Jstudner/jcorp-nomad/SD_Card_Template/Books/All Top Comics 6.jpg

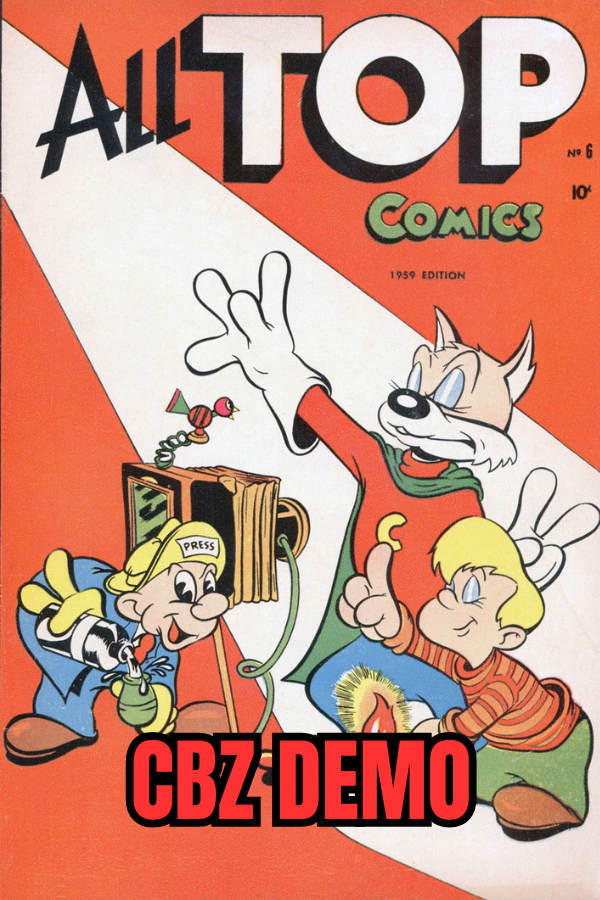
SD_Card_Template/Books/All Top Comics 6.jpg
