Jstudner/jcorp-nomad/SD_Card_Template/Books/MobyDick.jpg

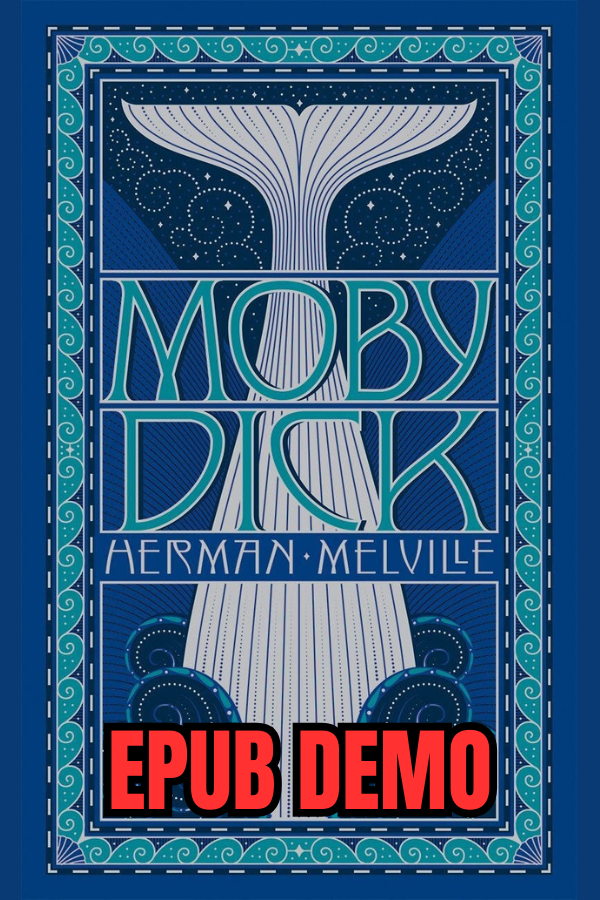
SD_Card_Template/Books/MobyDick.jpg
