Jstudner/jcorp-nomad/SD_Card_Template/Books/TheIliad.jpg

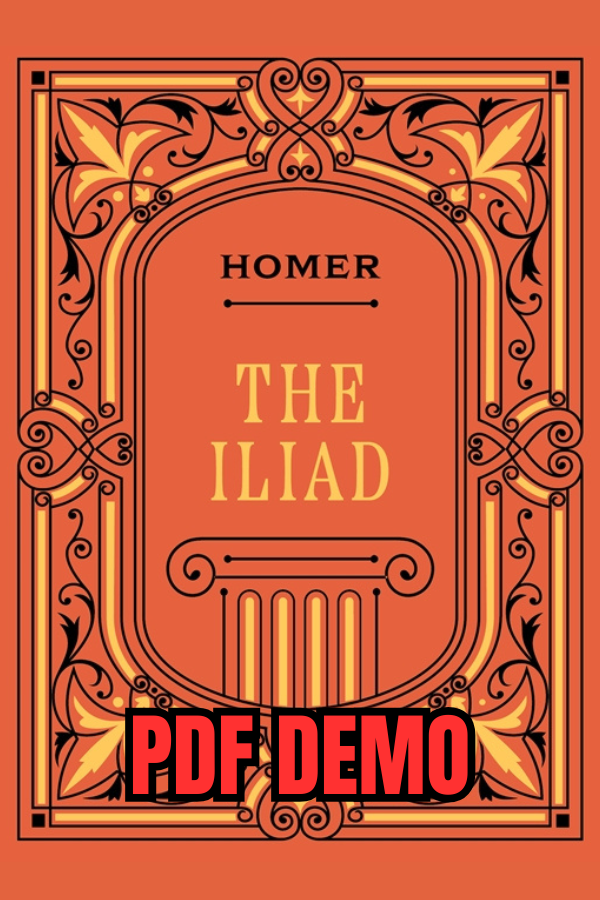
SD_Card_Template/Books/TheIliad.jpg
