Jstudner/jcorp-nomad/SD_Card_Template/Games/2048.png

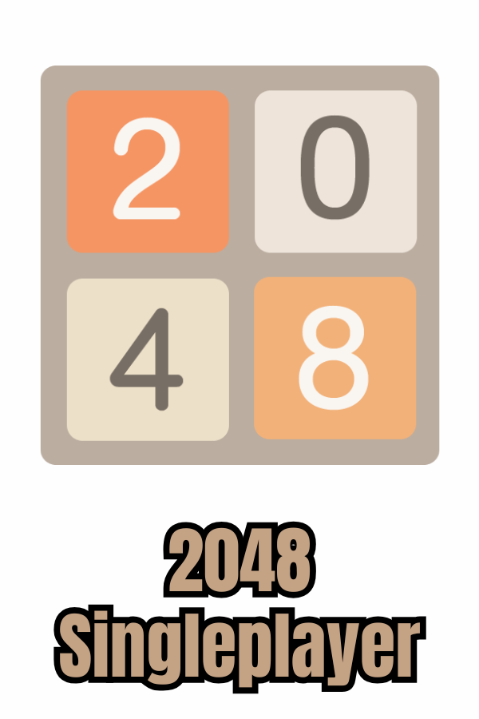
SD_Card_Template/Games/2048.png
