Jstudner/jcorp-nomad/SD_Card_Template/Games/Chess.png

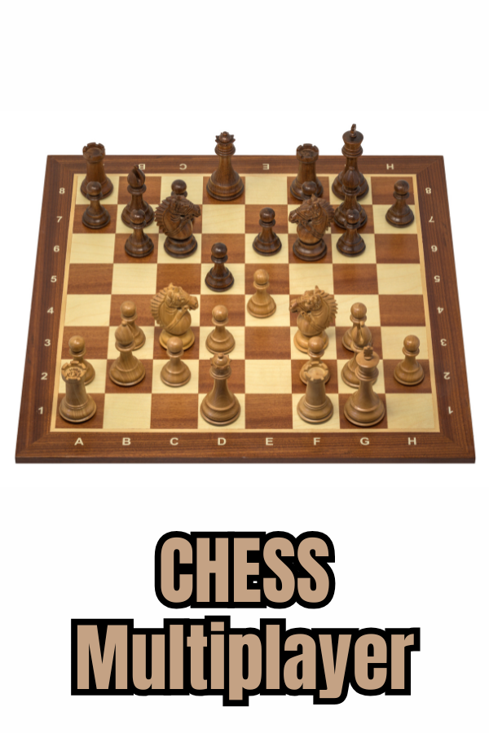
SD_Card_Template/Games/Chess.png
