Jstudner/jcorp-nomad/SD_Card_Template/Games/Connect Four.png

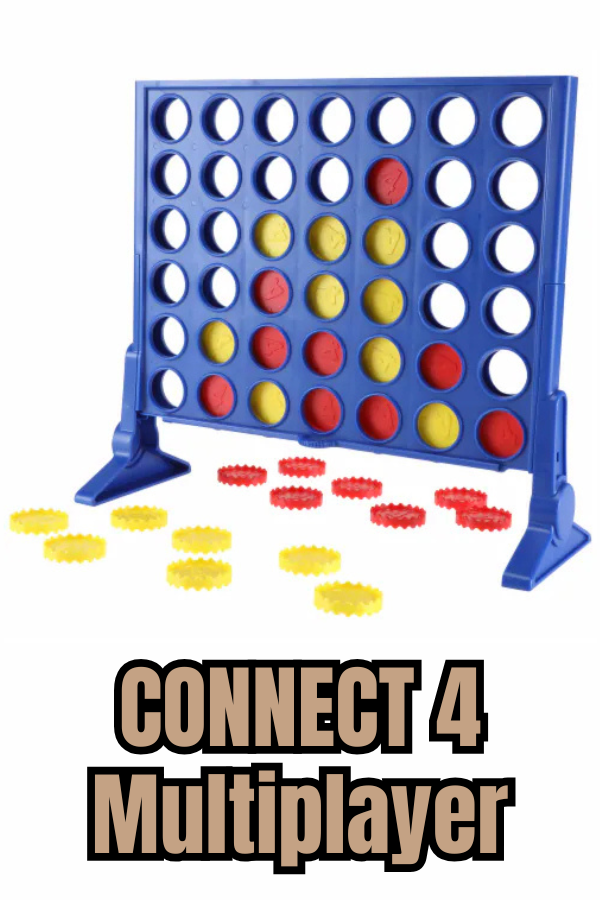
SD_Card_Template/Games/Connect Four.png
