Jstudner/jcorp-nomad/SD_Card_Template/Games/Crazy Eights.png

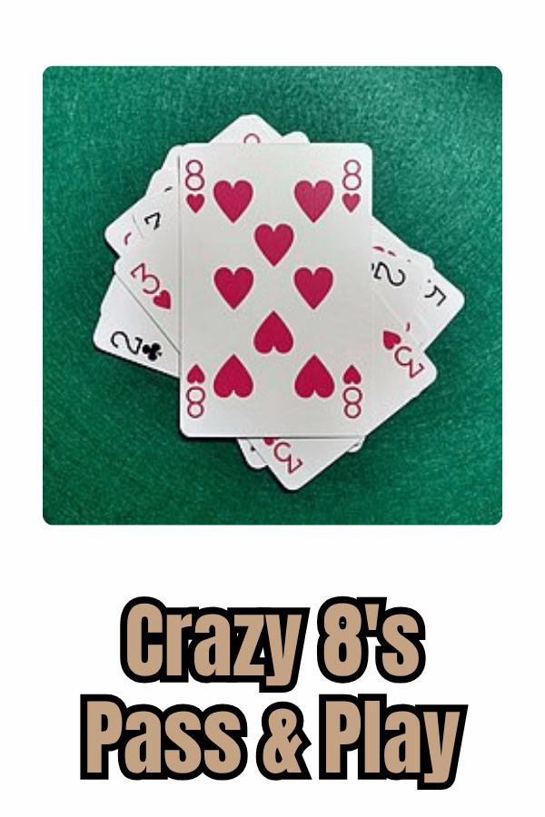
SD_Card_Template/Games/Crazy Eights.png
