Jstudner/jcorp-nomad/SD_Card_Template/Games/Doom.png

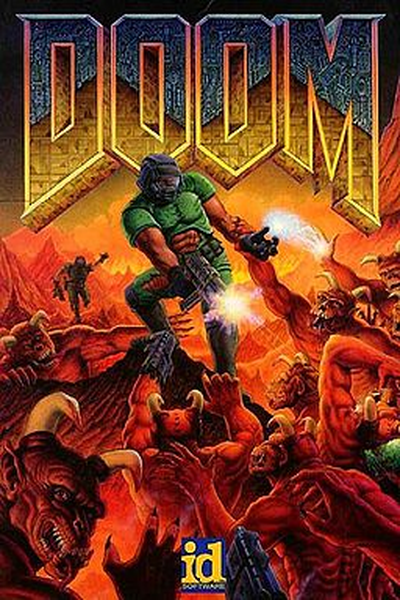
SD_Card_Template/Games/Doom.png
