Jstudner/jcorp-nomad/SD_Card_Template/Games/Dots and Boxes.png

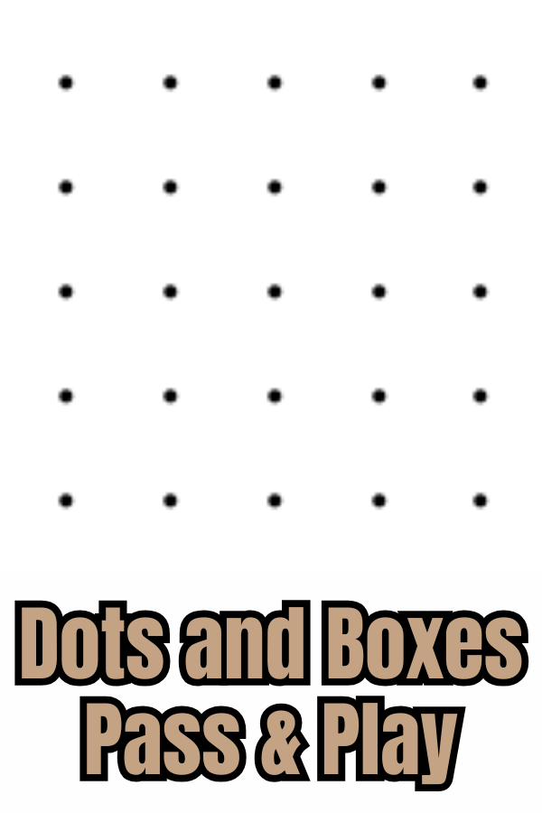
SD_Card_Template/Games/Dots and Boxes.png
