Jstudner/jcorp-nomad/SD_Card_Template/Games/Go.png

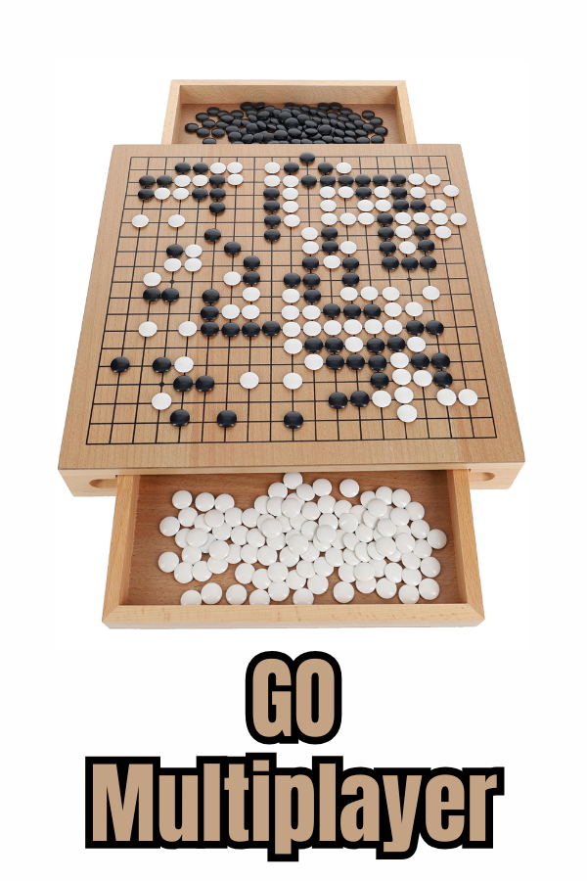
SD_Card_Template/Games/Go.png
