Jstudner/jcorp-nomad/SD_Card_Template/Games/Minesweeper.png

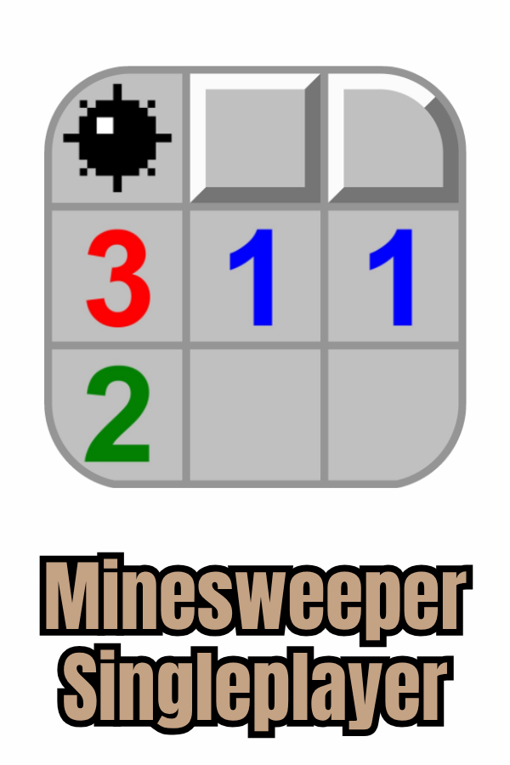
SD_Card_Template/Games/Minesweeper.png
