Jstudner/jcorp-nomad/SD_Card_Template/Games/Snake.png

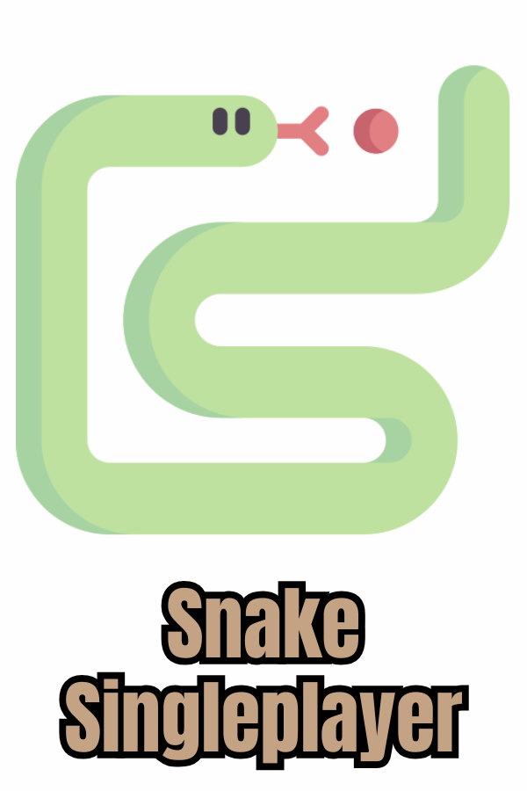
SD_Card_Template/Games/Snake.png
