Jstudner/jcorp-nomad/SD_Card_Template/Games/Tic-Tac-Toe.png

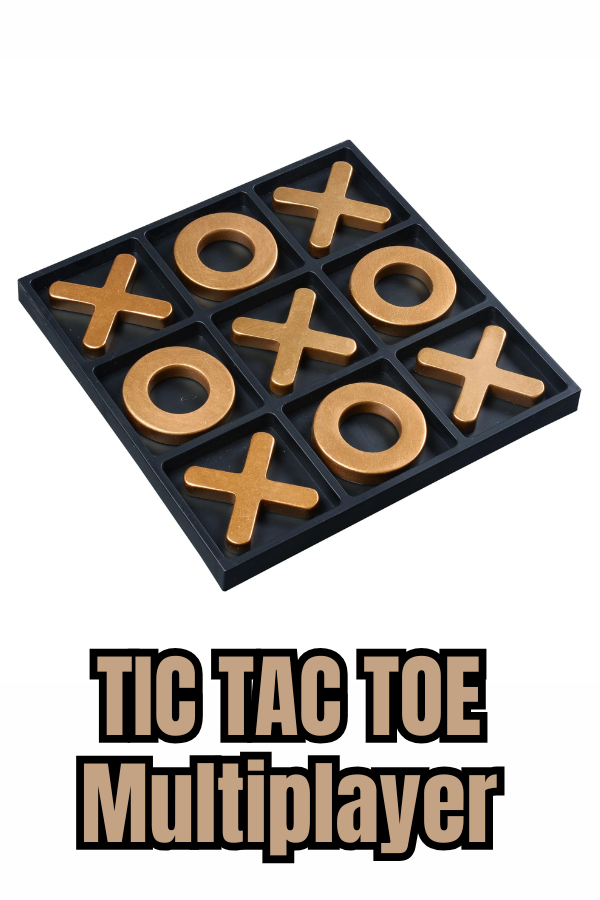
SD_Card_Template/Games/Tic-Tac-Toe.png
