Jstudner/jcorp-nomad/SD_Card_Template/Games/Whiteboard.png

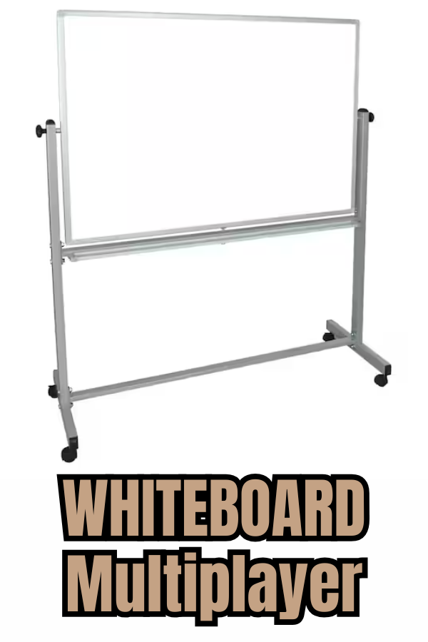
SD_Card_Template/Games/Whiteboard.png
