Jstudner/jcorp-nomad/SD_Card_Template/Maps/dc/tiles/10/292/391.jpg

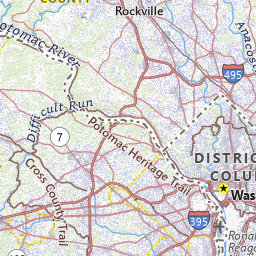
SD_Card_Template/Maps/dc/tiles/10/292/391.jpg
