Jstudner/jcorp-nomad/SD_Card_Template/Maps/dc/tiles/10/292/392.jpg

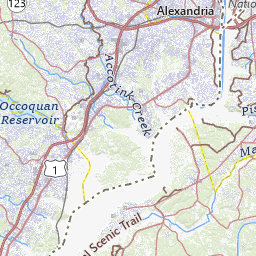
SD_Card_Template/Maps/dc/tiles/10/292/392.jpg
