Jstudner/jcorp-nomad/SD_Card_Template/Maps/dc/tiles/11/585/782.jpg

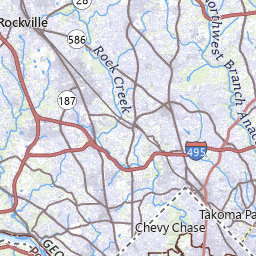
SD_Card_Template/Maps/dc/tiles/11/585/782.jpg
