Jstudner/jcorp-nomad/SD_Card_Template/Maps/dc/tiles/11/586/783.jpg

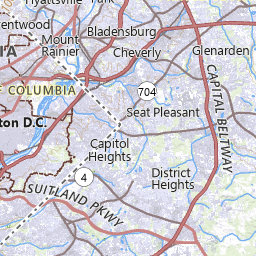
SD_Card_Template/Maps/dc/tiles/11/586/783.jpg
