Jstudner/jcorp-nomad/SD_Card_Template/Maps/dc/tiles/12/1170/1566.jpg

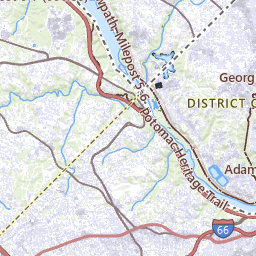
SD_Card_Template/Maps/dc/tiles/12/1170/1566.jpg
