Jstudner/jcorp-nomad/SD_Card_Template/Maps/dc/tiles/12/1171/1567.jpg

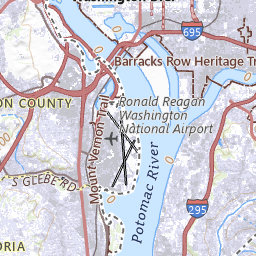
SD_Card_Template/Maps/dc/tiles/12/1171/1567.jpg
