Jstudner/jcorp-nomad/SD_Card_Template/Maps/dc/tiles/12/1172/1568.jpg

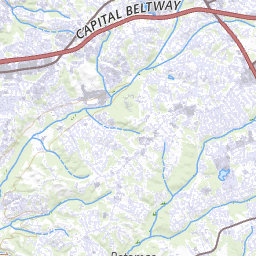
SD_Card_Template/Maps/dc/tiles/12/1172/1568.jpg
