Jstudner/jcorp-nomad/SD_Card_Template/Maps/dc/tiles/13/2342/3133.jpg

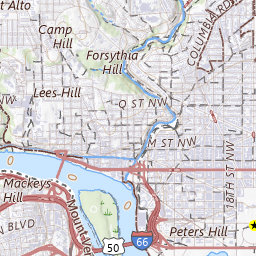
SD_Card_Template/Maps/dc/tiles/13/2342/3133.jpg
