Jstudner/jcorp-nomad/SD_Card_Template/Maps/dc/tiles/13/2344/3132.jpg

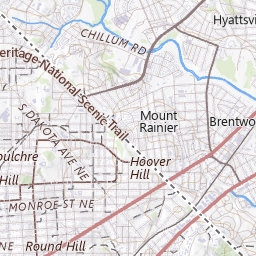
SD_Card_Template/Maps/dc/tiles/13/2344/3132.jpg
