Jstudner/jcorp-nomad/SD_Card_Template/Maps/dc/tiles/13/2345/3136.jpg

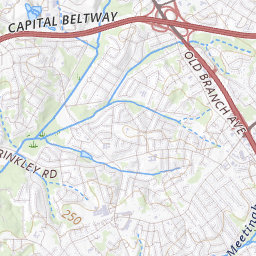
SD_Card_Template/Maps/dc/tiles/13/2345/3136.jpg
