Jstudner/jcorp-nomad/SD_Card_Template/Maps/dc/tiles/14/4683/6265.jpg

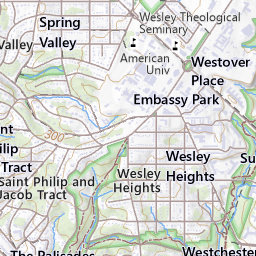
SD_Card_Template/Maps/dc/tiles/14/4683/6265.jpg
