Jstudner/jcorp-nomad/SD_Card_Template/Maps/dc/tiles/14/4684/6271.jpg

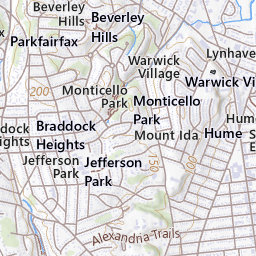
SD_Card_Template/Maps/dc/tiles/14/4684/6271.jpg
