Jstudner/jcorp-nomad/SD_Card_Template/Maps/dc/tiles/14/4686/6267.jpg

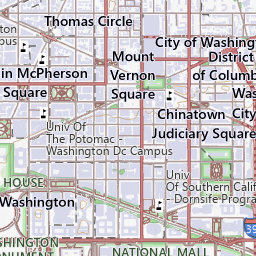
SD_Card_Template/Maps/dc/tiles/14/4686/6267.jpg
