Jstudner/jcorp-nomad/SD_Card_Template/Maps/dc/tiles/14/4687/6262.jpg

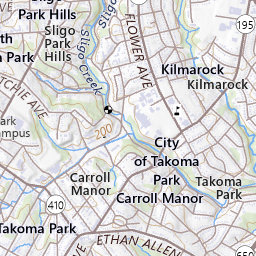
SD_Card_Template/Maps/dc/tiles/14/4687/6262.jpg
