Jstudner/jcorp-nomad/SD_Card_Template/Maps/dc/tiles/14/4688/6270.jpg

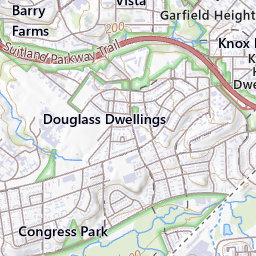
SD_Card_Template/Maps/dc/tiles/14/4688/6270.jpg
