Jstudner/jcorp-nomad/SD_Card_Template/Maps/dc/tiles/14/4689/6269.jpg

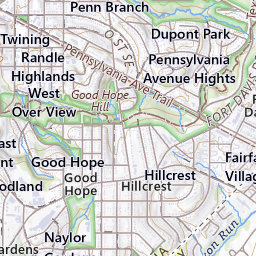
SD_Card_Template/Maps/dc/tiles/14/4689/6269.jpg
