Jstudner/jcorp-nomad/SD_Card_Template/Maps/dc/tiles/14/4691/6264.jpg

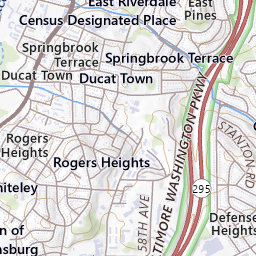
SD_Card_Template/Maps/dc/tiles/14/4691/6264.jpg
