Jstudner/jcorp-nomad/SD_Card_Template/Maps/dc/tiles/14/4691/6272.jpg

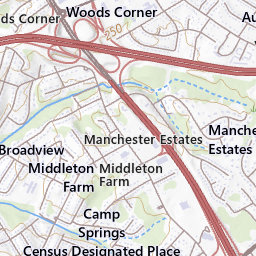
SD_Card_Template/Maps/dc/tiles/14/4691/6272.jpg
