Jstudner/jcorp-nomad/SD_Card_Template/Movies/The Phantom of The Opera.jpg

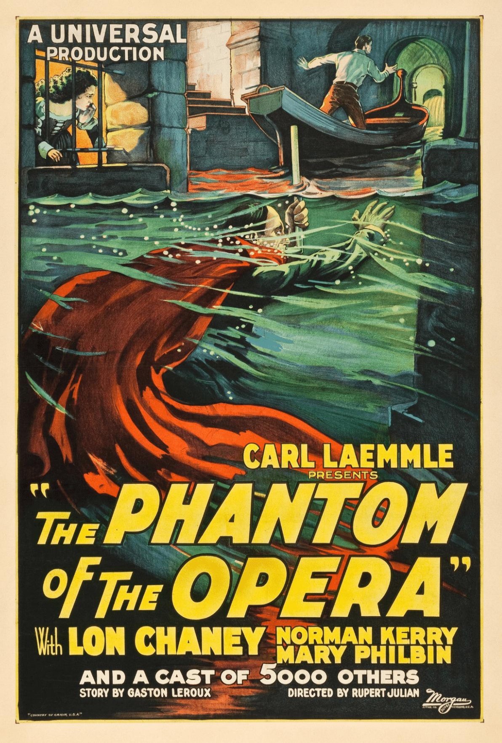
SD_Card_Template/Movies/The Phantom of The Opera.jpg
