Jstudner/jcorp-nomad/firmware/JcorpNomadProject/JcorpNomadProject.ino

// Jcorp Nomad Backend - exFAT edition
//<!-- Version 4.6 -->
//
// ---------------- board variant: set it in Display_ST7789.h ----------------
// USB-A, Waveshare ESP32-S3-LCD-1.47:  backlight GPIO 48, BOARD_USB_C 0 (default)
// USB-C, Waveshare ESP32-S3-LCD-1.47B: backlight GPIO 46, BOARD_USB_C 1
//
// that pin is the only firmware-visible difference between the two boards, and this
// file is byte-identical for both - checked against the flashing site's build tree.
//
// setting it here instead does nothing, and does it silently. the pin is used only in
// Display_ST7789.cpp, which is its own translation unit, so a define in the sketch
// never reaches it: with the define here Display_ST7789.cpp.o comes out identical to
// an unflagged build, the board keeps GPIO 48 and the screen just stays dark. edit the
// one line in Display_ST7789.h, or build with -DBOARD_USB_C=1.
#include <Arduino.h>
#include <WiFi.h>
#include <esp_netif.h>
#include <esp_heap_caps.h>
#include <AsyncTCP.h>
#include <ESPAsyncWebServer.h>
// NomadSD replaces SD_MMC: same pins and peripheral, SdFat underneath, so exFAT,
// FAT32 and FAT16 all mount. Included early because StreamHandle below holds a
// NomadFile64. NomadSD.h hides SdFat's headers, whose global `typedef FsFile File`
// would collide with fs::File.
#include "NomadSD.h"
#include "NomadDLNA.h"
#define SD_MMC NomadSD
#ifndef SD
#define SD NomadSD
#endif
#include "NomadDNS.h"
#include <ESPmDNS.h>
#include <ArduinoJson.h>
#include <map>
#include <time.h>
#include "Display_ST7789.h"
#include "LVGL_Driver.h"
#include "ui.h" 
#include "RGB_lamp.h"
#include <SPIFFS.h>
#include <Preferences.h>
#include "esp_wifi.h"
#include "esp_netif.h"      // esp_netif_dhcps_* -- restart softAP DHCP if it stays down (issue #126)
#include "esp_heap_caps.h"  // heap_caps_get_* -- DHCP-start heap logging
#if defined(ARDUINO_ARCH_ESP32)
  #include "soc/soc.h"
  #include "soc/rtc_cntl_reg.h"
  #include "esp_system.h"
  #include "esp_core_dump.h"
#endif
#include "esp32-hal-tinyusb.h"  // usb_persist_restart: the reliable road into ROM download mode
#include "usb_mode.h"
#include "boot_mode.h" // library for firmware switching

struct BreakdownStats {
  uint64_t bytes = 0;
  uint32_t files = 0;
  uint32_t dirs = 0;
};

void handleRangeRequest(AsyncWebServerRequest *request);
String urlDecode(const String& str);
void enqueueIndexUpdateForPath(const String& path);
void RGB_SetMode(uint8_t mode);
void applyRGBSettings();
String sanitizeToken(const String &s);
bool saveSettings();
String humanSize(size_t bytes);
extern void usb_setup();
extern void usb_loop();
#define BOOT_BUTTON_PIN 0
#include <vector>
#include <algorithm>
#include <atomic>
#ifndef GLOBAL_INDEX_BUF
#define GLOBAL_INDEX_BUF 1024
#endif
enum { HALF_INDEX_BUF = GLOBAL_INDEX_BUF / 2 };

static char g_lineBuf[GLOBAL_INDEX_BUF];
static uint8_t g_fileBuf[4096];                 // file reads/writes
static std::map<String, unsigned long> g_lastIndexSkipLog;
static inline void freeString(String &s) { s = String(); }
static inline void freeVectorString(std::vector<String> &v) { std::vector<String>().swap(v); }
static inline void freeVectorUInt32(std::vector<uint32_t> &v) { std::vector<uint32_t>().swap(v); }
static inline void closeFile(File &f) { if (f) f.close(); }

struct LvglMsg {
  char text[80];
  bool show;
};
static QueueHandle_t lvglQueue = NULL;

static void lvglSendMsg(const char *text, bool show) {
  if (!lvglQueue) return;
  LvglMsg m;
  m.show = show;
  if (text) {
    strncpy(m.text, text, sizeof(m.text) - 1);
    m.text[sizeof(m.text) - 1] = '\0';
  } else {
    m.text[0] = '\0';
  }
  xQueueSend(lvglQueue, &m, pdMS_TO_TICKS(50));
}

static void lvglDrainQueue() {
  if (!lvglQueue) return;
  LvglMsg msg;
  bool drainedAny = false;
  bool endedHidden = false;
  while (xQueueReceive(lvglQueue, &msg, 0) == pdTRUE) {
    if (msg.show) {
      lv_obj_clear_flag(ui_MediaGen, LV_OBJ_FLAG_HIDDEN);
      lv_textarea_set_text(ui_MediaGen, msg.text);
      endedHidden = false;
    } else {
      lv_textarea_set_text(ui_MediaGen, "");
      lv_obj_add_flag(ui_MediaGen, LV_OBJ_FLAG_HIDDEN);
      endedHidden = true;
    }
    drainedAny = true;
  }
  //only redraws the screen after all updates are done, removed the spinner (reloading constantly.. whoops lol)
  if (drainedAny) {
    // if we just hid the overlay, redraw twice so no remnant is left behind
    if (endedHidden) {
      lv_obj_invalidate(lv_scr_act());
      lv_timer_handler();
    }
    lv_timer_handler();
  }
}

static volatile bool bootButtonPressed = false;
// /flash-mode sets this; loop() does the actual switch (LVGL + restart must
// not run on the async_tcp task)
static volatile bool g_enterFlashMode = false;
#ifndef INDEX_MIN_HEAP
#define INDEX_MIN_HEAP 15000UL
#endif
static inline bool enoughHeapForIndex(size_t estNeededBytes = 20000) {
  size_t freeHeap = ESP.getFreeHeap();
  if (freeHeap < (INDEX_MIN_HEAP + estNeededBytes)) {
    Serial.printf("[Index] Not enough heap for index work (free=%u, need~%u). Deferring.\n",
                  (unsigned)freeHeap, (unsigned)(INDEX_MIN_HEAP + estNeededBytes));
    return false;
  }
  return true;
}
static size_t jsonEscapeToBuf(const String &in, char *dst, size_t dstLen) {
  if (!dst || dstLen == 0) return 0;
  size_t pos = 0;
  for (size_t i = 0; i < in.length() && pos + 1 < dstLen; ++i) {
    char c = in.charAt(i);
    if (c == '\\' || c == '\"') {
      if (pos + 2 >= dstLen) break;
      dst[pos++] = '\\';
      dst[pos++] = c;
    } else if (c == '\n') {
      if (pos + 2 >= dstLen) break;
      dst[pos++] = '\\';
      dst[pos++] = 'n';
    } else if (c == '\r') {
      if (pos + 2 >= dstLen) break;
      dst[pos++] = '\\';
      dst[pos++] = 'r';
    } else {
      dst[pos++] = c;
    }
  }
  dst[pos] = '\0';
  return pos;
}

static void writeIndexEntryToFile(File &fout, char t, const String &name, const String &path, uint64_t sz = 0, uint64_t mt = 0) {
  char escName[HALF_INDEX_BUF];
  char escPath[HALF_INDEX_BUF];
  jsonEscapeToBuf(name, escName, HALF_INDEX_BUF);
  jsonEscapeToBuf(path, escPath, HALF_INDEX_BUF);

  int pos = snprintf(g_lineBuf, GLOBAL_INDEX_BUF,
                     "{\"t\":\"%c\",\"n\":\"%s\",\"p\":\"%s\"", t, escName, escPath);
  if (pos < 0) pos = 0;
  if (t == 'f') {
    pos += snprintf(g_lineBuf + pos, (pos < (int)GLOBAL_INDEX_BUF) ? (GLOBAL_INDEX_BUF - pos) : 0,
                    ",\"sz\":%llu,\"mt\":%llu}\n",
                    (unsigned long long)sz, (unsigned long long)mt);
  } else {
    pos += snprintf(g_lineBuf + pos, (pos < (int)GLOBAL_INDEX_BUF) ? (GLOBAL_INDEX_BUF - pos) : 0,
                    "}\n");
  }

  size_t wlen = strlen(g_lineBuf);
  if (wlen) fout.write((const uint8_t*)g_lineBuf, wlen);
}
int screenBrightness = 100; // 0-100, default full brightness
void handleConnector(AsyncWebServerRequest *request);
unsigned long lastTempReading = 0;
float currentTempC = 0.0;
volatile bool mediaStreamingActive = false; // Flag to indicate active media streaming
volatile unsigned long lastStreamIoMs = 0;  // last time a streaming request/fill touched the SD
static bool sdScanned = false;
const uint32_t SD_SCAN_DELAY = 5000;  // milliseconds after boot
SemaphoreHandle_t sdMutex = NULL;
#include <map>
static uint32_t nextStreamId = 1;
// NomadFile64 rather than fs::File, so streams can seek and size past 4 GB on
// exFAT. Identical behaviour on FAT32. Move-only, like the SdFat handle.
struct StreamHandle {
  NomadFile64 file;
  String path;
  unsigned long lastActivity;
  uint64_t lastEndByte;
};
static std::map<uint32_t, StreamHandle> streamingFiles;
static std::map<String, uint32_t> streamPathIndex;
static SemaphoreHandle_t streamingFilesMutex = NULL;
static const int MAX_CONCURRENT_STREAMS = 8;

// close a handle we opened but never sent, so it doesn't leak until the LRU gets it
static void closeStreamById(uint32_t streamId) {
  if (!streamId) return;
  bool locked = (!streamingFilesMutex) ||
                (xSemaphoreTake(streamingFilesMutex, pdMS_TO_TICKS(300)) == pdTRUE);
  if (!locked) return;
  auto it = streamingFiles.find(streamId);
  if (it != streamingFiles.end()) {
    streamPathIndex.erase(it->second.path);
    it->second.file.close();
    streamingFiles.erase(it);
  }
  if (streamingFilesMutex) xSemaphoreGive(streamingFilesMutex);
}

static uint64_t cachedTotalBytes = 0;
static uint64_t cachedUsedBytes = 0;
static bool g_sdStatTrusted = false;
const char* SD_USAGE_FILE = "/.system-index/sd_usage.json";
static unsigned long lastScanTime = 0;
volatile bool sdbarDirty = false;
volatile int activeStreams = 0;
struct IndexBuildArgs {
  String dir;   // directory path to build index for (ex: "/Music/Album")
  String out;   // output index filename
};
static QueueHandle_t indexQueue = nullptr;

// Task management for performance optimization
TaskHandle_t indexWorkerTaskHandle = nullptr;
TaskHandle_t storageMonitorTaskHandle = nullptr;
volatile bool shutdownBackgroundTasks = false;
volatile bool indexingTasksActive = false;
String currentIndexingPath = "";
// Progress tracker for active indexing task
int g_currentBucketNum = 0;
int g_totalBucketsForProgress = 0;
int g_indexProgressPercent = 0;
SemaphoreHandle_t indexingPathMutex = NULL;

// ---- Multiplayer room store (HTTP polling, no WebSockets) ----
// Fixed-size plain char buffers, no Arduino String anywhere in this store or its
// handlers, and no SD I/O. Same class of hazard that caused heap corruption via
// unsynchronized Strings shared across tasks. Everything here is guarded by gameMutex.
#define MP_MAX_ROOMS 4
#define MP_CODE_LEN 5      // 4-char room code + NUL
#define MP_GAME_LEN 16     // e.g. "tictactoe", "chess"
#define MP_TOKEN_LEN 9     // 8 hex chars + NUL
#define MP_STATE_LEN 512   // opaque client-owned state blob (chess FEN ~90B, TTT ~32B)
#define MP_ROOM_IDLE_MS (2UL * 60UL * 1000UL)  // idle rooms are reclaimed after ~2 min

struct MpRoom {
  bool active;
  char code[MP_CODE_LEN];
  char game[MP_GAME_LEN];
  char token[2][MP_TOKEN_LEN];  // seat 0/1 tokens; empty string = seat open
  char state[MP_STATE_LEN];
  uint32_t seq;
  uint32_t games;               // finished games, used to alternate who starts a rematch
  unsigned long lastMs;
};
static MpRoom mpRooms[MP_MAX_ROOMS];
SemaphoreHandle_t gameMutex = NULL;

// Function declarations for task management
void shutdownBackgroundTasksForStreaming();
void startBackgroundTasksIfNeeded();
void checkStreamingTimeout();
void immediateEnqueueTopLevelTask(void *param);
void triggerIndexingIfNeeded(const String& filePath);
// Last time UI bar was updated
unsigned long lastSdbarUpdate = 0;
void updateSDBAR() {
  sdbarDirty = true;
}
void updateSDBAR_UI_ThreadOnly() {
  if (cachedTotalBytes == 0) return;
  
  int usage = (int)((cachedUsedBytes * 100) / cachedTotalBytes);
  if (usage > 100) usage = 100;
  if (usage < 0) usage = 0;
  
  lv_bar_set_value(ui_sdbar, usage, LV_ANIM_OFF);
  sdbarDirty = false;
}
#include <string> // used by std::map key
static std::map<std::string, unsigned long> lastIndexRequestMs;
const unsigned long INDEX_REQUEUE_COALESCE_MS = 2000UL; // 2 seconds coalescing
const size_t INDEX_REQUEST_MAP_EVICT_THRESHOLD = 200;       // prune once the map grows this large
const unsigned long INDEX_REQUEST_MAP_MAX_AGE_MS = 60000UL; // entries older than this are stale
static bool shouldCoalesceIndexRequest(const String &path) {
  std::string k(path.c_str());
  unsigned long now = millis();
  auto it = lastIndexRequestMs.find(k);
  if (it != lastIndexRequestMs.end()) {
    if (now - it->second < INDEX_REQUEUE_COALESCE_MS) {
      return false;
    }
  }
  lastIndexRequestMs[k] = now;

  if (lastIndexRequestMs.size() > INDEX_REQUEST_MAP_EVICT_THRESHOLD) {
    for (auto mit = lastIndexRequestMs.begin(); mit != lastIndexRequestMs.end(); ) {
      if (now - mit->second > INDEX_REQUEST_MAP_MAX_AGE_MS) {
        mit = lastIndexRequestMs.erase(mit);
      } else {
        ++mit;
      }
    }
  }
  return true;
}

// Helper: get parent directory for a path ("/Music/song.mp3" -> "/Music")
static String parentDirFromPath(const String &path) {
  if (path.length() == 0) return "/";
  int last = path.lastIndexOf('/');
  if (last <= 0) return "/"; // root or malformed -> treat as root
  String p = path.substring(0, last);
  if (p.length() == 0) return "/";
  return p;
}

// Paths that should never be indexed as media content. (generic SD card stuff that was causing some issues.)
static bool isFilesystemNoisePath(const String &path) {
  if (path.startsWith("/.system-index")) return true;      // our own index storage
  if (path.startsWith("/.")) return true;                  // hidden folders
  if (path.startsWith("/config")) return true;              // our own settings storage
  if (path.startsWith("/System Volume Information")) return true;
  if (path.startsWith("/$")) return true;                   // Windows/FAT system artifacts
  if (path.equalsIgnoreCase("/lost.dir")) return true;       // FAT filesystem recovery folder (Android/Linux)
  if (path.startsWith("/FOUND.")) return true;               // FAT32 chkdsk recovery folders (FOUND.000, FOUND.001, ...)
  if (path.equalsIgnoreCase("/RECYCLER")) return true;       // Windows recycle bin (older FAT)
  return false;
}

static bool shouldSkipIndexingPath(const String &path) {
  if (isFilesystemNoisePath(path)) return true;
  if (path.startsWith("/Archive")) return true;             // large ZIM archives, not media
  return false;
}

#define INDEXER_SLEEP_MS 300000 // 5 minutes between background scans
#define MAX_CLIENTS 8 // SoftAP max_connection; keep in sync with WiFi.softAP() calls below
String encodeIndexName(const String &path);

struct AdminSettings {
  String rgbMode = "off";
  String rgbColor = "#ff0000";
  String adminPassword = "";
  String wifiSSID = "Jcorp_Nomad";
  String wifiPassword = "password";
  int brightness = 100;            // percent 0-100 (Set_Backlight range); 230 was out-of-range and ignored
  bool autoGenerateMedia = true;   // check for new files on boot (default on)
  bool flipScreen = false;         // rotate LCD 180 deg (USB port upside down, e.g. car mounts)
  bool dlnaEnabled = true;         // TV support: DLNA server + SSDP discovery
  // WiFi Mode (station): join an existing network instead of running the hotspot.
  // staPersist=true -> try every boot (with hotspot fallback on failure).
  // staPersist=false -> only when the sta_once NVS flag is armed; a power cycle clears it.
  String staSSID = "";
  String staPassword = "";
  bool staPersist = false;
  // legacy wildcard captive DNS (answer every lookup with Nomad's address).
  // off = targeted responder, so phones keep using mobile data for the internet
  bool dnsCatchAll = false;
};

AdminSettings settings;
// Set by the /settings handler (async_tcp task); consumed by the task that owns
// LVGL flushes. MADCTL must never be written mid-flush from another task.
volatile bool lcdRotatePending = false;
const char* SETTINGS_PATH = "/config/settings.json";

// --- Admin session auth ---
// Not perfect, but designed to make it a bit more secure and properly gated, unlikly this will ever be needed, but some users want it as an option. 
String adminSessionToken = "";

String generateSessionToken() {
  char buf[33];
  for (int i = 0; i < 4; i++) {
    snprintf(buf + (i * 8), 9, "%08x", (unsigned)esp_random());
  }
  buf[32] = '\0';
  return String(buf);
}

bool isAdminAuthRequired() {
  return settings.adminPassword.length() > 0;
}

// Returns true if the request is allowed to perform an admin/state-changing action.
bool checkAdminAuth(AsyncWebServerRequest *request) {
  if (!isAdminAuthRequired()) return true; // admin password explicitly disabled
  if (adminSessionToken.length() == 0) return false; // nobody has logged in since boot
  if (!request->hasHeader("X-Admin-Token")) return false;
  return request->getHeader("X-Admin-Token")->value().equals(adminSessionToken);
}

// Web Console Logging System
#define MAX_LOG_ENTRIES 50
struct LogEntry {
  String message;
  String type;
  unsigned long timestamp;
};

LogEntry webLogs[MAX_LOG_ENTRIES];
int logIndex = 0;
int logCount = 0;
// guards webLogs[], lots of tasks write it and /console-logs reads it. unsynced
// String read/writes race the heap and panic. made in setup() before the server,
// so early boot logs (NULL mutex) skip locking safely
SemaphoreHandle_t webLogMutex = NULL;

// Function to add log entry for web console
void webLog(const String& message, const String& type = "info") {
  bool locked = (webLogMutex && xSemaphoreTake(webLogMutex, pdMS_TO_TICKS(50)) == pdTRUE);

  // if the reader has the lock, just go to serial instead of writing unsynced
  if (locked || !webLogMutex) {
    webLogs[logIndex].message = message;
    webLogs[logIndex].type = type;
    webLogs[logIndex].timestamp = millis();

    logIndex = (logIndex + 1) % MAX_LOG_ENTRIES;
    if (logCount < MAX_LOG_ENTRIES) {
      logCount++;
    }
  }

  if (locked) xSemaphoreGive(webLogMutex);

  // Also send to serial for debugging (always, lock or not)
  Serial.println(message);
}

// Function for formatted web logging
void webLogf(const String& type, const char* format, ...) {
  char buffer[256];
  va_list args;
  va_start(args, format);
  vsnprintf(buffer, sizeof(buffer), format, args);
  va_end(args);

  webLog(String(buffer), type);
}
#define SD_CLK_PIN 14
#define SD_CMD_PIN 15
#define SD_D0_PIN 16
#define SD_D1_PIN 18
#define SD_D2_PIN 17
#define SD_D3_PIN 21
const char *INDEX_DIR = "/.system-index";   // on-SD folder for index files
const size_t INDEX_WRITE_CHUNK = 4096;      // flush buffer when larger than this
// Normalize path: ensure leading '/', remove trailing '/'
String normalizePath(const String &p_in){
  if (p_in.length() == 0) return "/";
  String p = p_in;
  if (!p.startsWith("/")) p = "/" + p;
  while (p.length() > 1 && p.endsWith("/")) p = p.substring(0, p.length()-1);
  return p;
}
String encodeIndexName(const String &path_in) {
  String p = path_in;
  if (p.length() == 0) return String("root");

  // normalize leading/trailing slashes
  if (p.startsWith("/")) p = p.substring(1);
  while (p.length() > 1 && p.endsWith("/")) p = p.substring(0, p.length()-1);
  if (p.length() == 0) return String("root");

  // split on slashes and sanitize each segment
  std::vector<String> parts;
  String cur;
  for (size_t i = 0; i < p.length(); ++i) {
    char c = p.charAt(i);
    if (c == '/') {
      if (cur.length()) parts.push_back(cur);
      cur = "";
    } else {
      cur += c;
    }
  }
  if (cur.length()) parts.push_back(cur);

  // build encoded name joined by "__"
  String out;
  for (size_t i = 0; i < parts.size(); ++i) {
    String tok = sanitizeToken(parts[i]);
    if (tok.length() == 0) tok = "_";
    if (i) out += "__";
    out += tok;
  }
  if (out.length() == 0) out = "root";
  return out;
}
// Sanitize a directory name into a filename token (keeps alnum, - and _, else underscore)
String sanitizeToken(const String &s){
  String out;
  out.reserve(s.length());
  for (size_t i = 0; i < s.length(); ++i) {
    char c = s.charAt(i);
    if ((c >= 'a' && c <= 'z') || (c >= 'A' && c <= 'Z') || (c >= '0' && c <= '9')) out += c;
    else if (c == '-' || c == '_') out += c;
    else out += '_';
  }
  return out;
}

// Minimal JSON escape used for NDJSON fields
String jsonEscape(const String &in){
  String out;
  out.reserve(in.length() + 8);
  for (size_t i = 0; i < in.length(); ++i) {
    char c = in.charAt(i);
    if (c == '\\' || c == '\"') { out += '\\'; out += c; }
    else if (c == '\n') out += "\\n";
    else if (c == '\r') out += "\\r";
    else out += c;
  }
  return out;
}

// Build NDJSON header line: {"_type":"dir","path":"/X","sig":"hex","count":N}
String buildIndexHeader(const String &path, const String &sigHex, uint32_t count){
  String h;
  h.reserve(128);
  h += "{\"_type\":\"dir\",\"path\":\"";
  h += jsonEscape(path);
  h += "\",\"sig\":\"";
  h += sigHex;
  h += "\",\"count\":";
  h += String(count);
  h += "}\n";
  return h;
}

// Append one NDJSON entry (t: 'f'|'d', n: filename, p: absolute path, optional sz/mt)
String buildIndexEntry(const char t, const String &name, const String &path, uint64_t sz=0, uint64_t mt=0){
  String line;
  line.reserve(160);
  line += "{\"t\":\"";
  line += t;
  line += "\",\"n\":\"";
  line += jsonEscape(name);
  line += "\",\"p\":\"";
  line += jsonEscape(path);
  if (t == 'f') {
    line += "\",\"sz\":";
    line += String((unsigned long long)sz);
    line += ",\"mt\":";
    line += String((unsigned long long)mt);
    line += "}\n";
  } else {
    line += "\"}\n";
  }
  return line;
}

#define MAX_NESTED_AUTOGEN_ITEMS 40
bool readIndexHeaderSig(const String &indexPath, String &outSig, uint32_t &outCount) {
  outSig = "";
  outCount = 0;
  if (!SD_MMC.exists(indexPath)) return false;
  File f = SD_MMC.open(indexPath, FILE_READ);
  if (!f) return false;
  String header = f.readStringUntil('\n');
  f.close();
  if (header.length() == 0) return false;

  // Parse small JSON header
  StaticJsonDocument<256> doc;
  DeserializationError err = deserializeJson(doc, header);
  if (err) return false;
  const char* sig = doc["sig"];
  if (sig) outSig = String(sig);
  outCount = (uint32_t)(doc["count"] | doc["count"]); // header key is "count"
  return true;
}
// ---------- Media file detector + safe recursive counter ----------
static bool isMediaFile(const String &lowerName) {
  int dot = lowerName.lastIndexOf('.');
  if (dot < 0) return false;
  String ext = lowerName.substring(dot); // includes the dot, e.g. ".mp4"

  // Video (playback generally reliable: mp4, mov, mkv, webm, m4v)
  if (ext == ".mp4"  || ext == ".mov"  || ext == ".mkv"  || ext == ".webm" || ext == ".m4v"
   || ext == ".ts"   || ext == ".m2ts") return true;

  // Audio (mp3/flac/wav plus common containers)
  if (ext == ".mp3"  || ext == ".flac" || ext == ".wav"  || ext == ".aac"  || ext == ".m4a"
   || ext == ".ogg"  || ext == ".opus") return true;

  // Images
  if (ext == ".jpg"  || ext == ".jpeg" || ext == ".png"  || ext == ".webp" || ext == ".avif"
   || ext == ".gif"  || ext == ".bmp"  || ext == ".tiff" || ext == ".tif"  || ext == ".heic") return true;

  // Books / Documents / Archives (PDF and EPUB primary,CBZ works, CBR will not)
  if (ext == ".pdf"  || ext == ".epub" || ext == ".txt"  || ext == ".html" || ext == ".htm"
   || ext == ".cbz"  || ext == ".cbr"  || ext == ".azw3" || ext == ".mobi") return true;

  // Other video containers we count (wont work, dont use these dummy): .avi, .flv, .rmvb
  if (ext == ".avi" || ext == ".flv" || ext == ".rmvb") return true;

  return false;
}
static bool isComicFolder(const String &dirPath) {
  File d = SD_MMC.open(dirPath);
  if (!d || !d.isDirectory()) {
    if (d) d.close();
    return false;
  }
  
  bool hasImages = false;
  bool hasBookFiles = false;
  int imageCount = 0;
  
  d.rewindDirectory();
  File e;
  while ((e = d.openNextFile())) {
    if (e.isDirectory()) {
      e.close();
      continue;
    }
    
    String name = String(e.name());
    int lastSlash = name.lastIndexOf('/');
    if (lastSlash >= 0) name = name.substring(lastSlash + 1);
    name.toLowerCase();
    
    if (name.endsWith(".pdf") || name.endsWith(".epub") || 
        name.endsWith(".azw3") || name.endsWith(".mobi") ||
        name.endsWith(".mp3") || name.endsWith(".m4a") || 
        name.endsWith(".m4b") || name.endsWith(".flac")) {
      hasBookFiles = true;
      e.close();
      break;
    }
    
    if (name.endsWith(".png") || name.endsWith(".jpg") || 
        name.endsWith(".jpeg") || name.endsWith(".webp")) {
      hasImages = true;
      imageCount++;
    }
    
    e.close();
  }
  
  d.close();
  
  return hasImages && !hasBookFiles && imageCount >= 3;
}

static bool isBookFormat(const String &name) {
  String lower = name;
  lower.toLowerCase();
  return lower.endsWith(".pdf") || lower.endsWith(".epub") || 
         lower.endsWith(".azw3") || lower.endsWith(".mobi");
}
unsigned int countMediaFiles(const String &dirPath) {
  unsigned int count = 0;

  File d = SD_MMC.open(dirPath);
  if (!d || !d.isDirectory()) {
    if (d) d.close();
    return 0;
  }

  d.rewindDirectory();
  File e;
  while ((e = d.openNextFile())) {
    if (e.isDirectory()) {
      // name() is just the bare name under NomadSD. recursing on it opens the
      // wrong directory and silently counts nothing.
      String sub = String(e.path());
      count += countMediaFiles(sub);
    } else {
      // Lower-case filename once for efficient extension checks
      String name = String(e.name());
      name.toLowerCase();

      if (isMediaFile(name)) {
        ++count;
      }
    }
    e.close();
    yield(); // keep watchdog happy during recursion/long scans
  }

  d.close();
  return count;
}

// compatibility wrapper, some callers expect countDirItems()
unsigned int countDirItems(const String &p) {
  return countMediaFiles(p);
}

// Ensure INDEX_DIR exists (creates it if missing.. usualy)
void ensureIndexDir(){
  if (!SD_MMC.exists(INDEX_DIR)) {
    if (!SD_MMC.mkdir(INDEX_DIR)) {
      Serial.printf("[Index] Failed to create index dir %s\n", INDEX_DIR);
    } else {
      Serial.printf("[Index] Created index dir %s\n", INDEX_DIR);
    }
  }
}

// FNV-1a 64-bit hash incremental update (used to compute signature)
uint64_t fnv1a64_update(uint64_t h, const String &s){
  const uint64_t FNV_PRIME = 0x100000001b3ULL;
  uint64_t hash = h;
  for (size_t i = 0; i < s.length(); ++i) {
    hash ^= (uint8_t)s[i];
    hash *= FNV_PRIME;
  }
  return hash;
}

// Rename or copy fallback: try rename first, if that fails try copy & remove.
bool renameOrCopy(const String &src, const String &dst) {
  if (SD_MMC.exists(dst)) SD_MMC.remove(dst);
  if (SD_MMC.rename(src, dst)) return true;

  File fsrc = SD_MMC.open(src, FILE_READ);
  if (!fsrc) return false;
  File fdst = SD_MMC.open(dst, FILE_WRITE);
  if (!fdst) { fsrc.close(); return false; }

  uint8_t buf[512];
  while (fsrc.available()) {
    size_t r = fsrc.read(buf, sizeof(buf));
    if (r > 0) fdst.write(buf, r);
  }
  fsrc.close();
  fdst.close();
  SD_MMC.remove(src);
  return true;
}

// Atomic write helper - writes tmp then moves to final (uses renameOrCopy)
bool atomicWriteFile(const String &tmpPath, const String &finalPath) {
  // final renameOrCopy already does the heavy lifting; here just ensure final exists
  return renameOrCopy(tmpPath, finalPath);
}
void dumpSDRoot() {
  Serial.println("[Index] dumpSDRoot(): listing /");
  File r = SD_MMC.open("/");
  if (!r) {
    Serial.println("[Index] dumpSDRoot(): FAILED to open root '/'");
    return;
  }
  r.rewindDirectory();
  while (true) {
    File e = r.openNextFile();
    if (!e) break;
    Serial.printf("[Index] root-entry: %s %s\n", e.name(), e.isDirectory() ? "(dir)" : "(file)");
  }
  r.close();
}
bool writeNDIndexForDir(const String &dirPath, const String &outFilename) {
  // Acquire SD card mutex to prevent concurrent access
  if (sdMutex && xSemaphoreTake(sdMutex, pdMS_TO_TICKS(5000)) != pdTRUE) {
    Serial.printf("[Index] Mutex timeout for writeNDIndexForDir('%s')\n", dirPath.c_str());
    return false;
  }
  // Tracks whether this task currently holds sdMutex. 
  bool mutexHeld = true;

  // ensure index folder exists
  if (!SD_MMC.exists(INDEX_DIR)) SD_MMC.mkdir(INDEX_DIR);

  if (!enoughHeapForIndex()) {
    Serial.printf("[Index] Skipping index for '%s' due to low memory (free=%u)\n",
    dirPath.c_str(), (unsigned)ESP.getFreeHeap());
    if (sdMutex && mutexHeld) xSemaphoreGive(sdMutex);
    return false;
  }

// Normalize target dir
  String normPath = dirPath;
  if (!normPath.startsWith("/")) normPath = "/" + normPath;
  normPath = normalizePath(normPath);

  Serial.printf("[Index] Building index for '%s' (free heap=%u)\n", normPath.c_str(), (unsigned)ESP.getFreeHeap());
  webLogf("indexing_progress", "Starting indexing for '%s'", normPath.c_str());
  if (!SD_MMC.exists(normPath)) {
    Serial.printf("[Index] Path does not exist: %s\n", normPath.c_str());
    if (sdMutex && mutexHeld) xSemaphoreGive(sdMutex);
    return false;
  }

  // Open once to verify directory
  File root = SD_MMC.open(normPath);
  if (!root || !root.isDirectory()) {
    if (root) root.close();
    Serial.printf("[Index] Not a directory: %s\n", normPath.c_str());
    if (sdMutex && mutexHeld) xSemaphoreGive(sdMutex);
    return false;
  }
  root.close();

   // Determine recursion strategy based on path
  bool isRoot = (normPath == "/");
  bool isShows = (normPath == "/Shows");
  bool isShowSubfolder = normPath.startsWith("/Shows/") && normPath.indexOf('/', 7) < 0;
  bool isShowSeasonFolder = normPath.startsWith("/Shows/") && normPath.indexOf('/', 7) > 0;
  bool isMusicSubfolder = normPath.startsWith("/Music/");
  bool isBooks = (normPath == "/Books");
  bool isBooksSubfolder = normPath.startsWith("/Books/") && normPath.indexOf('/', 7) < 0;
  bool isBooksComicFolder = normPath.startsWith("/Books/") && normPath.indexOf('/', 7) > 0;
  int maxDepth = 10;

  if (isRoot) {
    maxDepth = 0;
  } else if (isBooks) {
    maxDepth = 0;
  } else if (isBooksSubfolder) {
    maxDepth = 0;
  } else if (isBooksComicFolder) {
    maxDepth = 0;
  }

  Serial.printf("[Index] Recursion depth for '%s': %d\n", normPath.c_str(), maxDepth);
  // Prepass: compute signature and total count
  uint64_t sig = 0xcbf29ce484222325ULL;
  unsigned long count = 0;
  unsigned long writeCount = 0; // mirrors 'count' but tracked separately during writepass
  bool abortIndex = false;

  // soft caps so a huge/slow dir aborts instead of running forever
  const unsigned long MAX_INDEX_ITEMS = 20000;
  const unsigned long MAX_INDEX_BUILD_MS = 120000; // 2 minutes
  unsigned long buildStartMs = millis();

  std::function<void(const String&, int)> prepass = [&](const String &path, int depth) {
    vTaskDelay(pdMS_TO_TICKS(1));
    // Stop recursion if we've hit max depth or if abort flag is set
    if (abortIndex || depth > maxDepth) return;

    // Skip system/hidden folders
    if (shouldSkipIndexingPath(path)) {
    Serial.printf("[Index] Skipping folder: %s\n", path.c_str());
    return;
    }

    if (path.startsWith("/Books/") && isComicFolder(path)) {
    Serial.printf("[Index] Detected comic folder, skipping contents: %s\n", path.c_str());
    return;
    }

    File d = SD_MMC.open(path);
    if (!d || !d.isDirectory()) { if (d) d.close(); return; }
    vTaskDelay(pdMS_TO_TICKS(1));
    d.rewindDirectory();

    int itemCount = 0;
    while (true) {
    if (abortIndex) break;

    if (count > MAX_INDEX_ITEMS || (millis() - buildStartMs) > MAX_INDEX_BUILD_MS) {
      Serial.printf("[Index] Aborting prepass for '%s': safety limit reached (count=%lu, elapsed=%lums)\n",
                    normPath.c_str(), count, (unsigned long)(millis() - buildStartMs));
      webLogf("warning", "Indexing '%s' aborted - directory too large or taking too long", normPath.c_str());
      abortIndex = true;
      break;
    }

    File e = d.openNextFile();
    if (!e) break;

    String full = String(e.name());
    // Normalize full path for consistency
    if (!full.startsWith("/")) full = normalizePath(path + "/" + full);
    else full = normalizePath(full);

    int ls = full.lastIndexOf('/');
    String tail = (ls >= 0) ? full.substring(ls + 1) : full;

    // Skip hidden files/folders
    if (tail.startsWith(".")) {
    e.close();
    continue;
    }

    if (e.isDirectory()) {
    sig = fnv1a64_update(sig, full + "|" + tail);
    ++count;
    e.close();
    // Recurse with depth tracking
    prepass(full, depth + 1);
    } else {
    uint64_t fsz = (uint64_t)e.size();
    uint64_t fmt = 0;
    sig = fnv1a64_update(sig, full + "|" + String(fsz) + "|" + String(fmt));
    ++count;
    e.close();
    }

    // Yield more frequently to prevent WDT and keep device responsive
    if (++itemCount % 5 == 0) {
    vTaskDelay(pdMS_TO_TICKS(3));
    if (sdMutex) {
      xSemaphoreGive(sdMutex);
      mutexHeld = false;
      vTaskDelay(pdMS_TO_TICKS(10));
      if (xSemaphoreTake(sdMutex, pdMS_TO_TICKS(10000)) != pdTRUE) {
        Serial.printf("[Index] Lost mutex during prepass, aborting\n");
        abortIndex = true;
        d.close();
        return;
      }
      mutexHeld = true;
    }
    }
    }

    d.close();
  };

  prepass(normPath, 0);  // Start at depth 0

  if (abortIndex) {
    Serial.printf("[Index] Aborted index for '%s' during prepass (mutex loss or safety limit, count so far=%lu, free heap=%u)\n",
                  normPath.c_str(), count, (unsigned)ESP.getFreeHeap());
    if (sdMutex && mutexHeld) xSemaphoreGive(sdMutex);
    return false;
  }

  Serial.printf("[Index] Prepass complete for '%s': %lu items, free heap=%u\n",
                normPath.c_str(), count, (unsigned)ESP.getFreeHeap());

  // Prepare files
  String tmpPath   = String(INDEX_DIR) + "/" + outFilename + ".tmp";
  String finalPath = String(INDEX_DIR) + "/" + outFilename;

  char sigHex[17];
  snprintf(sigHex, sizeof(sigHex), "%016llx", (unsigned long long)sig);

  // if nothing changed since last build, skip the rewrite. reading the header sig
  // is basically free vs rewriting the whole file. (yay)
  {
    String oldSig;
    uint32_t oldCount = 0;
    if (readIndexHeaderSig(finalPath, oldSig, oldCount) &&
        oldSig.equalsIgnoreCase(sigHex) && oldCount == (uint32_t)count) {
      Serial.printf("[Index] Unchanged, skipping rewrite for '%s' (count=%lu, sig=%s)\n",
                    normPath.c_str(), count, sigHex);
      if (sdMutex && mutexHeld) xSemaphoreGive(sdMutex);
      return true;
    }
  }

  File fout = SD_MMC.open(tmpPath, FILE_WRITE);
  if (!fout) {
    Serial.printf("[Index] FAILED to open tmp for write: %s\n", tmpPath.c_str());
    if (sdMutex && mutexHeld) xSemaphoreGive(sdMutex);
    return false;
  }

  // Write header line
  String header = buildIndexHeader(normPath, String(sigHex), count);
  fout.write((const uint8_t*)header.c_str(), header.length());

  // second pass: write entries. everyone funnels through here so the throttled
  // screen progress below covers full scans, queue items and manual reindexes
  unsigned long lastIndexScreenUpdateMs = 0;
  std::function<void(const String&, int)> writepass = [&](const String &path, int depth) {
    vTaskDelay(pdMS_TO_TICKS(1));
    if (abortIndex || depth > maxDepth) return;

    if (shouldSkipIndexingPath(path)) return;

    if (path.startsWith("/Books/") && isComicFolder(path)) return;

    File d = SD_MMC.open(path);
    if (!d || !d.isDirectory()) { if (d) d.close(); return; }
    vTaskDelay(pdMS_TO_TICKS(1));
    d.rewindDirectory();

    int itemCount = 0;
    while (true) {
    if (abortIndex) break;

    if (writeCount > MAX_INDEX_ITEMS || (millis() - buildStartMs) > MAX_INDEX_BUILD_MS) {
      Serial.printf("[Index] Aborting writepass for '%s': safety limit reached (count=%lu, elapsed=%lums)\n",
                    normPath.c_str(), writeCount, (unsigned long)(millis() - buildStartMs));
      webLogf("warning", "Indexing '%s' aborted - directory too large or taking too long", normPath.c_str());
      abortIndex = true;
      fout.close();
      SD_MMC.remove(tmpPath);
      break;
    }

    File e = d.openNextFile();
    if (!e) break;
    ++writeCount;

    // throttled to 1500ms (not per-item) so it cant flood the small lvglQueue
    unsigned long nowMsForScreen = millis();
    if (nowMsForScreen - lastIndexScreenUpdateMs > 1500) {
      lastIndexScreenUpdateMs = nowMsForScreen;
      char screenBuf[80];
      snprintf(screenBuf, sizeof(screenBuf), "Indexing: %s\n%lu items\n\nDo not unplug!",
               normPath.c_str(), writeCount);
      lvglSendMsg(screenBuf, true);
    }

    String full = String(e.name());
    if (!full.startsWith("/")) full = normalizePath(path + "/" + full);
    else full = normalizePath(full);

    int ls = full.lastIndexOf('/');
    String tail = (ls >= 0) ? full.substring(ls + 1) : full;

    if (tail.startsWith(".")) {
    e.close();
    continue;
    }

    char entryType = e.isDirectory() ? 'd' : 'f';

    char escName[HALF_INDEX_BUF];
    char escPath[HALF_INDEX_BUF];
    jsonEscapeToBuf(tail, escName, HALF_INDEX_BUF);
    jsonEscapeToBuf(full, escPath, HALF_INDEX_BUF);

    if (entryType == 'f') {
    // size() saturates at SIZE_MAX rather than wrapping; only then pay for the
    // 64-bit lookup, so normal files (and every FAT32 card) cost nothing extra
    uint64_t fsz = (uint64_t)e.size();
    if (fsz == (uint64_t)SIZE_MAX) fsz = SD_MMC.fileSize64(full.c_str());
    uint64_t fmt = 0;
    int pos = snprintf(g_lineBuf, GLOBAL_INDEX_BUF,
    "{\"t\":\"f\",\"n\":\"%s\",\"p\":\"%s\",\"sz\":%llu,\"mt\":%llu}\n",
    escName, escPath, (unsigned long long)fsz, (unsigned long long)fmt);
    if (pos < 0) pos = 0;
    size_t wlen = strlen(g_lineBuf);
    if (wlen) fout.write((const uint8_t*)g_lineBuf, wlen);
    } else {
    bool isComic = full.startsWith("/Books/") && isComicFolder(full);
    int pos = snprintf(g_lineBuf, GLOBAL_INDEX_BUF,
    "{\"t\":\"d\",\"n\":\"%s\",\"p\":\"%s\"%s}\n",
    escName, escPath, isComic ? ",\"comic\":true" : "");
    if (pos < 0) pos = 0;
    size_t wlen = strlen(g_lineBuf);
    if (wlen) fout.write((const uint8_t*)g_lineBuf, wlen);
    }

    if (entryType == 'd') {
    e.close();
    writepass(full, depth + 1);
    } else {
    e.close();
    }

    if (++itemCount % 5 == 0) {
    vTaskDelay(pdMS_TO_TICKS(3));
    if (sdMutex) {
      xSemaphoreGive(sdMutex);
      mutexHeld = false;
      vTaskDelay(pdMS_TO_TICKS(10));
      if (xSemaphoreTake(sdMutex, pdMS_TO_TICKS(10000)) != pdTRUE) {
        Serial.printf("[Index] Lost mutex during writepass, aborting\n");
        abortIndex = true;
        d.close();
        fout.close();
        SD_MMC.remove(tmpPath);
        return;
      }
      mutexHeld = true;
    }
    }
    }

    d.close();
  };

  writepass(normPath, 0);

  if (abortIndex) {
    Serial.printf("[Index] Aborted writepass for '%s' (mutex loss or safety limit, written so far=%lu, free heap=%u)\n",
                  normPath.c_str(), writeCount, (unsigned)ESP.getFreeHeap());
    if (sdMutex && mutexHeld) xSemaphoreGive(sdMutex);
    return false;
  }

  fout.flush();
  fout.close();

  String newFinal = finalPath + ".new";
  if (SD_MMC.exists(newFinal)) SD_MMC.remove(newFinal);

  bool moved = SD_MMC.rename(tmpPath, newFinal);
  if (!moved) {
    File fsrc = SD_MMC.open(tmpPath, FILE_READ);
    if (fsrc) {
    File fdst = SD_MMC.open(newFinal, FILE_WRITE);
    if (fdst) {
    uint8_t buf[512];
    while (fsrc.available()) {
    size_t r = fsrc.read(buf, sizeof(buf));
    if (r > 0) fdst.write(buf, r);
    }
    fsrc.close();
    fdst.close();
    SD_MMC.remove(tmpPath);
    moved = true;
    } else {
    fsrc.close();
    }
    }
  }

  if (!moved) {
    Serial.printf("[Index] FAILED staging -> %s from tmp %s\n", newFinal.c_str(), tmpPath.c_str());
    SD_MMC.remove(tmpPath);
    if (sdMutex && mutexHeld) xSemaphoreGive(sdMutex);
    return false;
  }

  if (SD_MMC.exists(finalPath)) SD_MMC.remove(finalPath);

  if (!SD_MMC.rename(newFinal, finalPath)) {
    if (!renameOrCopy(newFinal, finalPath)) {
    Serial.printf("[Index] FAILED atomic replace %s -> %s\n", newFinal.c_str(), finalPath.c_str());
    SD_MMC.remove(newFinal);
    webLogf("error", "Failed atomic replace %s -> %s", newFinal.c_str(), finalPath.c_str());
    if (sdMutex && mutexHeld) xSemaphoreGive(sdMutex);
    return false;
    } else {
    SD_MMC.remove(newFinal);
    }
  }

  Serial.printf("[Index] Built index %s for %s (count=%lu, sig=%s, maxDepth=%d)\n",
    outFilename.c_str(), normPath.c_str(), count, sigHex, maxDepth);
  webLogf("completed_index_logging", "Completed indexing '%s' - %lu items processed", normPath.c_str(), count);

    String metaFilename = outFilename;
    if (metaFilename.endsWith(".ndjson")) {
    metaFilename = metaFilename.substring(0, metaFilename.length() - 7); // remove ".ndjson"
    }
    metaFilename += ".meta";
    String metaPath = String(INDEX_DIR) + "/" + metaFilename;

    File metaFile = SD_MMC.open(metaPath, FILE_WRITE);
    if (metaFile) {
    // Write JSON meta with path, count, and signature
    metaFile.print("{\"path\":\"");
    metaFile.print(jsonEscape(normPath));
    metaFile.print("\",\"count\":");
    metaFile.print(count);
    metaFile.print(",\"sig\":\"");
    metaFile.print(sigHex);
    metaFile.println("\"}");
    metaFile.close();
    Serial.printf("[Index] Wrote meta file %s\n", metaFilename.c_str());
    } else {
    Serial.printf("[Index] WARNING: Failed to write meta file %s\n", metaFilename.c_str());
    }

    if (sdMutex && mutexHeld) xSemaphoreGive(sdMutex);
    return true;
}

// ---------------- write bucket-level index ----------------
// write top-level bucket index (ex: /Music -> Music.index.ndjson)
bool writeBucketIndex(const String &bucketPath) {
  String name = bucketPath;
  if (name.startsWith("/")) name = name.substring(1);
  int slash = name.indexOf('/');
  if (slash >= 0) name = name.substring(0, slash);
  if (!name.length()) name = "root";
  String outFile = String(name) + ".index.ndjson";
  return writeNDIndexForDir(bucketPath, outFile);
}

// Build bucket index convenience wrapper (returns true on success)
bool buildBucketIndex(const String &bucketPath) {
  String bucket = bucketPath;
  if (bucket.startsWith("/")) bucket = bucket.substring(1);
  if (bucket.endsWith("/")) bucket = bucket.substring(0, bucket.length()-1);
  if (bucket.length() == 0) bucket = "root";
  String outFilename = bucket + ".index.ndjson";

  bool ok = writeNDIndexForDir(bucketPath, outFilename);
  if (ok) {
    Serial.printf("[Index] Built bucket index %s for %s\n", outFilename.c_str(), bucketPath.c_str());
    webLogf("completed_index_logging", "Completed indexing bucket '%s' - wrote %s", bucketPath.c_str(), outFilename.c_str());
    return true;
  }
  Serial.printf("[Index] Failed building bucket index for %s\n", bucketPath.c_str());
  return false;
}
String urlencode(String str) {
  String encoded = "";
  char c;
  char code0, code1;
  char code[] = "0123456789ABCDEF";

  for (int i = 0; i < str.length(); i++) {
    c = str.charAt(i);
    if (isalnum(c)) {
      encoded += c;
    } else {
      code0 = code[(c >> 4) & 0xF];
      code1 = code[c & 0xF];
      encoded += '%';
      encoded += code0;
      encoded += code1;
    }
  }
  return encoded;
}
// Settings Setup:
bool loadSettings() {
  if (sdMutex && xSemaphoreTake(sdMutex, pdMS_TO_TICKS(3000)) != pdTRUE) {
    Serial.println("[Settings] Mutex timeout in loadSettings");
    return false;
  }

  if (!SD_MMC.exists(SETTINGS_PATH)) {
    Serial.println("Settings file not found. Generating default.");
    if (sdMutex) xSemaphoreGive(sdMutex);
    return saveSettings();  // Save defaults
  }

  File file = SD_MMC.open(SETTINGS_PATH);
  if (!file || file.isDirectory()) {
    Serial.println("Failed to open settings file.");
    if (sdMutex) xSemaphoreGive(sdMutex);
    return false;
  }

  StaticJsonDocument<768> doc;
  DeserializationError error = deserializeJson(doc, file);
  file.close();

  if (sdMutex) xSemaphoreGive(sdMutex);

  if (error) {
    Serial.println("Failed to parse settings JSON.");
    return false;
  }

  settings.rgbMode = doc["rgbMode"] | "off";
  settings.rgbColor = doc["rgbColor"] | "#ff0000";
  settings.adminPassword = doc["adminPassword"] | "";
  settings.wifiSSID = doc["wifiSSID"] | "Jcorp_Nomad";
  settings.wifiPassword = doc["wifiPassword"] | "password";
  settings.brightness = doc["brightness"] | 100;
  // brightness is 0-100 (Set_Backlight ignores >100). old builds defaulted to 230, clamp it
  settings.brightness = constrain(settings.brightness, 0, 100);
  settings.autoGenerateMedia = doc["autoGenerateMedia"] | true;   // default on if unset
  settings.flipScreen = doc["flipScreen"] | false;
  settings.dlnaEnabled = doc["dlnaEnabled"] | true;
  settings.staSSID = doc["staSSID"] | "";
  settings.staPassword = doc["staPassword"] | "";
  settings.staPersist = doc["staPersist"] | false;
  settings.dnsCatchAll = doc["dnsCatchAll"] | false;

  return true;
}
// ---------------- deferred config writes ----------------
// Writing a file on the async_tcp task stalls the web server while the filesystem
// hunts for free clusters, and on a nearly full card that trips the task watchdog.
// Small config writes go through this queue and a background task does the SD work.
struct ConfigWriteJob {
  String path;
  String content;
};
QueueHandle_t cfgWriteQueue = NULL;

// atomic temp+rename write, only ever runs on the writer task
static bool writeFileAtomicBlocking(const String &path, const String &content) {
  if (sdMutex && xSemaphoreTake(sdMutex, pdMS_TO_TICKS(15000)) != pdTRUE) {
    Serial.printf("[CFGW] SD busy too long, write of %s dropped\n", path.c_str());
    return false;
  }
  int slash = path.lastIndexOf('/');
  if (slash > 0) SD_MMC.mkdir(path.substring(0, slash));
  String tempPath = path + ".tmp";
  bool ok = false;
  File f = SD_MMC.open(tempPath, FILE_WRITE);
  if (f) {
    size_t n = f.write((const uint8_t *)content.c_str(), content.length());
    f.close();
    if (n == content.length()) {
      if (SD_MMC.exists(path)) SD_MMC.remove(path);
      ok = SD_MMC.rename(tempPath, path);
    }
    if (!ok) SD_MMC.remove(tempPath);
  }
  if (sdMutex) xSemaphoreGive(sdMutex);
  if (ok) Serial.printf("[CFGW] wrote %s (%u bytes)\n", path.c_str(), (unsigned)content.length());
  else webLogf("error", "Config write failed: %s", path.c_str());
  return ok;
}

void configWriterTask(void *param) {
  ConfigWriteJob *job = NULL;
  for (;;) {
    if (xQueueReceive(cfgWriteQueue, &job, portMAX_DELAY) == pdTRUE && job) {
      bool ok = writeFileAtomicBlocking(job->path, job->content);
      // /save writes land here, so a page that writes a file into a content bucket
      // (the cookbook editor) has to refresh that folder's index or the new file
      // stays invisible until the next full scan. Enqueued after the write, not in
      // the request handler, or the rebuild can race the file into existence.
      // Non-bucket paths (settings, .system-ui.json) are ignored by the callee.
      if (ok) triggerIndexingIfNeeded(job->path);
      delete job;
      job = NULL;
      vTaskDelay(pdMS_TO_TICKS(20));
    }
  }
}

// Queue a write. False means the queue is full or not created yet; boot
// context callers can safely write inline since they are not on async_tcp.
bool queueConfigWrite(const String &path, const String &content) {
  if (!cfgWriteQueue) return false;
  ConfigWriteJob *job = new ConfigWriteJob{ path, content };
  if (xQueueSend(cfgWriteQueue, &job, pdMS_TO_TICKS(50)) != pdTRUE) {
    delete job;
    return false;
  }
  return true;
}

// ---------------- UI config (menu pages, downloads, uploads, motd) ----------------
// Owned by the firmware: held in RAM, served from RAM, written to /.system-ui.json
// through the config writer, changed only through the admin authed POST
// /api/ui-config. Pages that read the file directly still work.
const char *UI_CONFIG_PATH = "/.system-ui.json";
String g_uiConfigJson = "{}";
SemaphoreHandle_t uiCfgMutex = NULL;

void loadUiConfigFromSD() {
  if (!SD_MMC.exists(UI_CONFIG_PATH)) return;
  File f = SD_MMC.open(UI_CONFIG_PATH, FILE_READ);
  if (!f) return;
  String s = f.readString();
  f.close();
  s.trim();
  if (s.length() > 0 && s.length() < 4096) g_uiConfigJson = s;
}

bool saveSettings() {
  StaticJsonDocument<768> sdoc;
  sdoc["rgbMode"] = settings.rgbMode;
  sdoc["rgbColor"] = settings.rgbColor;
  sdoc["adminPassword"] = settings.adminPassword;
  sdoc["wifiSSID"] = settings.wifiSSID;
  sdoc["wifiPassword"] = settings.wifiPassword;
  sdoc["brightness"] = settings.brightness;
  sdoc["autoGenerateMedia"] = settings.autoGenerateMedia;
  sdoc["flipScreen"] = settings.flipScreen;
  sdoc["dlnaEnabled"] = settings.dlnaEnabled;
  sdoc["staSSID"] = settings.staSSID;
  sdoc["staPassword"] = settings.staPassword;
  sdoc["staPersist"] = settings.staPersist;
  sdoc["dnsCatchAll"] = settings.dnsCatchAll;
  String json;
  serializeJson(sdoc, json);

  // normal path: hand the write to the config writer so the caller (usually
  // a web handler on async_tcp) never blocks on the card
  if (queueConfigWrite(SETTINGS_PATH, json)) return true;

  // boot path, writer not running yet: write inline, this is not async_tcp
  SD_MMC.mkdir("/config"); // Ensure directory exists

  File file = SD_MMC.open(SETTINGS_PATH, FILE_WRITE);
  if (!file) {
    Serial.println("Failed to open settings file for writing.");
    return false;
  }

  StaticJsonDocument<768> doc;
  doc["rgbMode"] = settings.rgbMode;
  doc["rgbColor"] = settings.rgbColor;
  doc["adminPassword"] = settings.adminPassword;
  doc["wifiSSID"] = settings.wifiSSID;
  doc["wifiPassword"] = settings.wifiPassword;
  doc["brightness"] = settings.brightness;
  doc["autoGenerateMedia"] = settings.autoGenerateMedia;
  doc["flipScreen"] = settings.flipScreen;
  doc["dlnaEnabled"] = settings.dlnaEnabled;
  doc["staSSID"] = settings.staSSID;
  doc["staPassword"] = settings.staPassword;
  doc["staPersist"] = settings.staPersist;
  doc["dnsCatchAll"] = settings.dnsCatchAll;

  bool success = serializeJson(doc, file) > 0;
  file.close();
  return success;
}

// --------------- Media Generation Stuff ------------
bool isAlwaysGenerateEnabled() {
    return SD_MMC.exists("/always_generate.flag");
}

void enableAlwaysGenerate() {
    File f = SD_MMC.open("/always_generate.flag", FILE_WRITE);
    if (f) {
        f.print("1");
        f.close();
    }
}

void disableAlwaysGenerate() {
    SD_MMC.remove("/always_generate.flag");
}

bool isOneTimeGenerateRequested() {
    return SD_MMC.exists("/generate_once.flag");
}

void requestOneTimeGenerate() {
    File f = SD_MMC.open("/generate_once.flag", FILE_WRITE);
    if (f) {
        f.print("1");
        f.close();
    }
}

void clearOneTimeGenerate() {
    SD_MMC.remove("/generate_once.flag");
}
//------------------- delete recursive -------------
bool deleteRecursive(String path) {
  File entry = SD_MMC.open(path);
  if (!entry) return false;

  if (!entry.isDirectory()) {
    entry.close();
    return SD_MMC.remove(path);
  }

  File child;
  int n = 0;
  while ((child = entry.openNextFile())) {
    String childPath = String(path) + "/" + child.name();
    deleteRecursive(childPath);
    child.close();
    // deleting a season folder is hundreds of FAT chain frees in a row. without
    // a breather this hits the task watchdog on the async_tcp task.
    if (++n % 16 == 0) vTaskDelay(pdMS_TO_TICKS(1));
  }

  entry.close();
  return SD_MMC.rmdir(path);
}


// ───────────────── SD‑recovery globals ───────────────
volatile bool sdErrorFlag            = false;
unsigned long sdErrorCooldownUntil   = 0;

// Mount as fast as the board will reliably go, stepping down on failure. Media mode
// used to mount 1-bit at 20 MHz while USB mode ran 4-bit at 40 MHz on the same six
// pins, capping large reads at ~625 KB/s. The last rung matches the old settings so
// a board or card that cannot do 4-bit still comes up as before.
static const char *g_sdModeDesc = "not mounted";

bool mountSDCard() {
  struct { bool oneBit; int khz; const char *desc; } modes[] = {
    { false, SDMMC_FREQ_HIGHSPEED, "4-bit @ 40MHz" },
    { false, SDMMC_FREQ_DEFAULT,   "4-bit @ 20MHz" },
    { true,  SDMMC_FREQ_DEFAULT,   "1-bit @ 20MHz" },
  };
  for (unsigned i = 0; i < sizeof(modes) / sizeof(modes[0]); i++) {
    if (SD_MMC.begin("/sdcard", modes[i].oneBit, false, modes[i].khz, 12)) {
      g_sdModeDesc = modes[i].desc;
      Serial.printf("[SD] Mounted %s (%s)\n", modes[i].desc, NomadSD.fsTypeName());
      return true;
    }
    Serial.printf("[SD] Mount failed at %s, stepping down\n", modes[i].desc);
    SD_MMC.end();
    delay(200);
  }
  g_sdModeDesc = "not mounted";
  return false;
}

// No card at boot: say so on the little screen instead of sitting on "Booting..."
// forever, and keep probing. inserting the card restarts into a normal boot
static void sdBootHalt(const char *msg) {
  lv_obj_clear_flag(ui_MediaGen, LV_OBJ_FLAG_HIDDEN);
  lv_textarea_set_text(ui_MediaGen, msg);
  for (;;) {
    for (int i = 0; i < 100; ++i) { lv_timer_handler(); delay(30); }  // ~3s
    if (mountSDCard()) esp_restart();
  }
}

bool tryRecoverSDCard() {
    Serial.println("[SD] Attempting recovery…");

    // close streaming handles before unmounting, else an async fill on a dead
    // File is a use-after-free that reboots the device. lock order: streamingFilesMutex -> sdMutex
    if (streamingFilesMutex && xSemaphoreTake(streamingFilesMutex, pdMS_TO_TICKS(3000)) == pdTRUE) {
        bool sdHeld = (!sdMutex) || (xSemaphoreTake(sdMutex, pdMS_TO_TICKS(3000)) == pdTRUE);
        for (auto &kv : streamingFiles) kv.second.file.close();
        streamingFiles.clear();
        streamPathIndex.clear();
        activeStreams = 0;

        SD_MMC.end();          // unmount
        delay(1000);           // give hardware a breather
        bool ok = mountSDCard();

        if (sdHeld && sdMutex) xSemaphoreGive(sdMutex);
        xSemaphoreGive(streamingFilesMutex);
        Serial.println(ok ? "[SD] Recovery OK." : "[SD] Recovery failed.");
        return ok;
    }

    // couldnt get the stream map (something wedged holding it), remount under sdMutex alone.
    // give back only what we took - releasing a mutex we don't hold frees it under its owner
    bool sdTaken = (!sdMutex) || (xSemaphoreTake(sdMutex, pdMS_TO_TICKS(3000)) == pdTRUE);
    if (!sdTaken) Serial.println("[SD] Recovery: sdMutex timeout, remounting without it.");
    SD_MMC.end();
    delay(1000);
    bool ok = mountSDCard();
    if (sdMutex) xSemaphoreGive(sdMutex);
    Serial.println(ok ? "[SD] Recovery OK." : "[SD] Recovery failed.");
    return ok;
}

String rfc3339Now() {
  // no NTP/RTC offline, so fake it: fixed epoch + uptime so OPDS times at least move
  const time_t REFERENCE_EPOCH = 1752321600; // 2025-07-12T12:00:00Z
  time_t now = REFERENCE_EPOCH + (time_t)(millis() / 1000UL);
  struct tm t;
  gmtime_r(&now, &t);
  char buf[21];
  strftime(buf, sizeof(buf), "%Y-%m-%dT%H:%M:%SZ", &t);
  return String(buf);
}

// Captive DNS lives in NomadDNS.cpp (targeted responder, not a wildcard hijack)
AsyncWebServer server(80); // Web server on port 80
std::map<AsyncWebServerRequest*, File> activeUploads;
int connectedClients = 0;
// LED Mode and Color Helper Wrappers
uint8_t currentLEDMode = 0;  // 0=off, 1=rainbow, 2=solid color
uint8_t solidR = 0, solidG = 0, solidB = 0;
void RGB_SetColor(uint8_t r, uint8_t g, uint8_t b) {
    solidR = r;
    solidG = g;
    solidB = b;
    currentLEDMode = 2; 
    Set_Color(g, r, b);
}
extern lv_obj_t *ui_wifi;
extern lv_obj_t *ui_SDcard;
bool lastWifiStatus = false;
bool lastSDStatus = false;
//Globals for SD scan
unsigned long lastUpdateTime = 0;
volatile bool requestIndexing = false;     // set by admin endpoint; consumed by index worker
// true only when the boot change detector actually found changes and queued a reindex.
// this is the CHECK's result, not the toggle - a boot with no changes indexes nothing.
volatile bool bootReindexQueued = false;
volatile bool indexingInProgress = false;  // guard so we never run multiple index runs concurrently
volatile bool settingsReady = false;       // set to true after loadSettings() runs

// --- WiFi Mode (station) state ---
bool g_staMode = false;             // true = boot joined an existing network instead of running the hotspot
String g_staFailReason = "";        // why the last join attempt failed; written in setup() only, read by /api/wifi-mode
volatile uint32_t g_wifiModeRestartAt = 0;  // millis deadline for a deferred restart after a wifi-mode change; 0 = none

// every generated URL (OPDS, m3u, DLNA) uses this: the assigned STA address
// when joined to a home network, the AP address otherwise
IPAddress nomadLocalIP() {
  return g_staMode ? WiFi.localIP() : WiFi.softAPIP();
}

int maskToCidr(IPAddress mask) {
  uint32_t m = (uint32_t)mask;
  int bits = 0;
  while (m) { bits += m & 1; m >>= 1; }
  return bits;
}

// New scan/index coordination flags
volatile bool sdScanInProgress = false;    // true while SD scan is performing its initial pass
volatile bool sdScanCompleted = false;     // set to true after the initial SD scan completes

volatile bool bootIndexAllowed = true;   

unsigned long lastSDScanTime = 0;
const unsigned long SD_SCAN_INTERVAL = 60000; // 60 seconds

// ---------- background indexing control ----------

// Update the UI with the number of connected users
void updateUI(int userCount) {
    char buffer[10];
    snprintf(buffer, sizeof(buffer), "%d", userCount);
    lv_label_set_text(ui_userlabel, buffer);
}
void updateToggleStatus() {
    // hotspot: up = AP iface has its address. station: up = link to the home
    // network still held (the core auto-reconnects on drops)
    bool currentWifiStatus = g_staMode ? (WiFi.status() == WL_CONNECTED)
                                       : (bool)(uint32_t)WiFi.softAPIP();
    if (currentWifiStatus != lastWifiStatus) {
        if (currentWifiStatus) {
            lv_obj_add_state(ui_wifi, LV_STATE_CHECKED);
            if (!lastWifiStatus) {
                webLog(g_staMode ? "[SYSTEM] WiFi network link verified" : "[SYSTEM] WiFi AP verified successfully", "success");
            }
        } else {
            lv_obj_clear_state(ui_wifi, LV_STATE_CHECKED);
            webLog(g_staMode ? "[SYSTEM] WiFi network link lost - auto-reconnect running" : "[SYSTEM] WiFi AP failure detected - attempting recovery", "error");
        }
        lastWifiStatus = currentWifiStatus;
    }
}

void updateSDStatus() {
    bool currentSDStatus = SD_MMC.cardType() != CARD_NONE;
    if (currentSDStatus != lastSDStatus) {
        if (currentSDStatus) {
            lv_obj_add_state(ui_SDcard, LV_STATE_CHECKED);
            if (!lastSDStatus) {
                webLog("[SYSTEM] SD card verified successfully", "success");
            }
        } else {
            lv_obj_clear_state(ui_SDcard, LV_STATE_CHECKED);
            webLog("[SYSTEM] SD card failure detected - attempting recovery", "error");
        }
        lastSDStatus = currentSDStatus;
    }
}

// Stream a chunk of text to save RAM
void opdsWrite(AsyncResponseStream *s, const String &chunk) {
    s->print(chunk);
}
//(OPDS thing, MUST FIX THIS ITS SO BROKEN (STILL SO BROKEN, will update the paths to handle new library format... later...))
String xmlEscape(const String &in) {   
  String out;
  for (char c : in) {
    switch (c) {
      case '&':  out += "&amp;";  break;
      case '<':  out += "&lt;";   break;
      case '>':  out += "&gt;";   break;
      default:   out += c;        break;
    }
  }
  return out;
}

String slugify(const String &in) {        
  String out;
  for (char c : in) {
    if (isalnum(c))       out += (char)tolower(c);
    else if (c==' ' || c=='_' || c=='-') out += '-';
    // every other char is dropped
  }
  return out;
}

// Get a count of currently connected WiFi clients
void updateClientCount() {
    wifi_sta_list_t wifi_sta_list;
    if (esp_wifi_ap_get_sta_list(&wifi_sta_list) == ESP_OK) {
        connectedClients = wifi_sta_list.num;
        updateUI(connectedClients);
    }
}

// Utility: extract base name (no path, no extension)
String getFileBaseName(const String& name) {
    String base = name.substring(name.lastIndexOf('/') + 1);
    int dotIndex = base.lastIndexOf('.');
    if (dotIndex != -1) base = base.substring(0, dotIndex);
    return base;
}
bool isValidExtension(const String& filename, const std::vector<String>& exts) {
  String nameLower = filename;
  nameLower.toLowerCase();
  for (const auto& ext : exts) {
    if (nameLower.endsWith(ext)) return true;
  }
  return false;
}

void generateMediaJson(){
  webLog("[MEDIA] Starting media index generation for all buckets", "info");
  Serial.println("[Index] generateMediaJson() -> switched to NDJSON writer");
  webLogf("indexing_progress", "Starting full media index generation for all buckets");

  // ensure index dir
  ensureIndexDir();

  buildBucketIndex("/");       // writes root.index.ndjson
  webLogf("indexing_progress", "Completed indexing root bucket (/)");
  buildBucketIndex("/Movies"); // flat: files plus sidecar covers
  webLogf("indexing_progress", "Completed indexing Movies bucket");
  buildBucketIndex("/Shows");  // writes Shows.index.ndjson
  webLogf("indexing_progress", "Completed indexing Shows bucket");
  buildBucketIndex("/Music");  // writes Music.index.ndjson
  webLogf("indexing_progress", "Completed indexing Music bucket");
  buildBucketIndex("/Games");  // writes Games.index.ndjson (flat layout, no nested per-subfolder pass)
  webLogf("indexing_progress", "Completed indexing Games bucket");

File showsDir = SD.open("/Shows");
  if(showsDir){
    while(true){
    File s = showsDir.openNextFile();
    if(!s) break;
    if(s.isDirectory()){
    String showName = String(s.name());
    String showPath = "/Shows";
    if(!showPath.endsWith("/")) showPath += "/";
    showPath += showName;
    String fileToken = "Shows__" + sanitizeToken(showName) + ".nested.ndjson";
    writeNDIndexForDir(showPath, fileToken);
    Serial.printf("[Index] wrote per-show nested %s for %s\n", fileToken.c_str(), showPath.c_str());
    }
    s.close();
    }
    showsDir.close();
  }

  // Generate nested indexes for Music subfolders (Artist/Playlist level)
  File musicDir = SD.open("/Music");
  if(musicDir){
    while(true){
    File m = musicDir.openNextFile();
    if(!m) break;
    if(m.isDirectory()){
    String musicSubName = String(m.name());
    // Extract just the folder name (not full path)
    int lastSlash = musicSubName.lastIndexOf('/');
    if(lastSlash >= 0) musicSubName = musicSubName.substring(lastSlash + 1);
    
    String musicSubPath = "/Music/" + musicSubName;
    String fileToken = "Music__" + sanitizeToken(musicSubName) + ".nested.ndjson";
    writeNDIndexForDir(musicSubPath, fileToken);
    Serial.printf("[Index] wrote per-music-folder nested %s for %s\n", fileToken.c_str(), musicSubPath.c_str());
    }
    m.close();
    }
    musicDir.close();
  }

  buildBucketIndex("/Books");
  webLogf("indexing_progress", "Completed indexing Books bucket");
  
  File booksDir = SD.open("/Books");
  if(booksDir){
    while(true){
      File b = booksDir.openNextFile();
      if(!b) break;
      if(b.isDirectory()){
        String bookSubName = String(b.name());
        int lastSlash = bookSubName.lastIndexOf('/');
        if(lastSlash >= 0) bookSubName = bookSubName.substring(lastSlash + 1);
        
        String bookSubPath = "/Books/" + bookSubName;
        
        if (!isComicFolder(bookSubPath)) {
          String fileToken = "Books__" + sanitizeToken(bookSubName) + ".nested.ndjson";
          writeNDIndexForDir(bookSubPath, fileToken);
          Serial.printf("[Index] wrote per-books-folder nested %s for %s\n", fileToken.c_str(), bookSubPath.c_str());
        } else {
          Serial.printf("[Index] Skipping comic folder nested index: %s\n", bookSubPath.c_str());
        }
      }
      b.close();
    }
    booksDir.close();
  }
  // Gallery, Files, Cookbook and Workshop: flat bucket index plus one nested index per
  // first-level subfolder, same shape as Music. Deeper folders are answered live by
  // /listfiles, so one level is all the index needs.
  const char *extraBuckets[] = { "/Gallery", "/Files", "/Cookbook", "/Workshop", NULL };
  for (int eb = 0; extraBuckets[eb]; eb++) {
    String broot = extraBuckets[eb];
    buildBucketIndex(broot);
    webLogf("indexing_progress", "Completed indexing %s bucket", broot.c_str());
    File bdir = SD.open(broot);
    if (bdir) {
      while (true) {
        File d = bdir.openNextFile();
        if (!d) break;
        if (d.isDirectory()) {
          String subName = String(d.name());
          int lastSlash = subName.lastIndexOf('/');
          if (lastSlash >= 0) subName = subName.substring(lastSlash + 1);
          String subPath = broot + "/" + subName;
          String fileToken = broot.substring(1) + "__" + sanitizeToken(subName) + ".nested.ndjson";
          writeNDIndexForDir(subPath, fileToken);
          Serial.printf("[Index] wrote nested %s for %s\n", fileToken.c_str(), subPath.c_str());
        }
        d.close();
      }
      bdir.close();
    }
  }

  String summary = "{\n  \"generated\": true,\n  \"buckets\": {\n";
  // read index files to include counts
  File idx = SD.open(INDEX_DIR);
  if(idx){
    while(true){
      File f = idx.openNextFile();
      if(!f) break;
      String fname = String(f.name());
      if(fname.endsWith(".index.ndjson") || fname.endsWith(".nested.ndjson")){
        // read first line header
        String header = f.readStringUntil('\n');
        // try to parse count quickly by locating '"count":' substring
        int pos = header.indexOf("\"count\":");
        String countStr = "0";
        if(pos >= 0){
          int start = pos + 8;
          int end = start;
          while(end < header.length() && isDigit(header.charAt(end))) end++;
          countStr = header.substring(start, end);
        }
        summary += "    \"" + fname + "\": " + countStr + ",\n";
      }
      f.close();
    }
    idx.close();
  }
  if(summary.endsWith(",\n")) summary = summary.substring(0, summary.length()-2) + "\n";
  summary += "  }\n}\n";

  // write summary to /media.json (small)
  File mf = SD.open("/media.json", FILE_WRITE);
  if(mf){
    mf.print(summary);
    mf.close();
  } else {
    Serial.println("[Index] failed to write /media.json");
    webLogf("error", "Failed to write /media.json (card full or read-only?)");
  }

  webLog("[MEDIA] Media index generation completed successfully", "success");
  Serial.println("[Index] Media JSON generation complete");
}

String absURL(const String &path) {
    return "http://" + nomadLocalIP().toString() + path;
}


void handleOPDSRoot(AsyncWebServerRequest *request) {
    AsyncResponseStream *res = request->beginResponseStream(
        "application/atom+xml;profile=opds-catalog;kind=navigation");

    opdsWrite(res, "<?xml version=\"1.0\" encoding=\"utf-8\"?>\n"
                   "<feed xmlns=\"http://www.w3.org/2005/Atom\" "
                   "xmlns:opds=\"http://opds-spec.org/2010/catalog\">\n");

    opdsWrite(res, "  <id>urn:uuid:nomad-opds-root</id>\n"
                   "  <title>Nomad OPDS Catalog</title>\n"
                   "  <updated>2025-07-12T12:00:00Z</updated>\n"
                   "  <author><name>Nomad Server</name></author>\n");

    // Add required navigation links
    opdsWrite(res, "  <link rel=\"self\" href=\"" + absURL("/opds/root.xml") + "\" "
                   "type=\"application/atom+xml;profile=opds-catalog;kind=navigation\"/>\n");
    opdsWrite(res, "  <link rel=\"start\" href=\"" + absURL("/opds/root.xml") + "\" "
                   "type=\"application/atom+xml;profile=opds-catalog;kind=navigation\"/>\n");

    opdsWrite(res, "  <entry>\n"
                   "    <title>All Books</title>\n"
                   "    <id>urn:uuid:nomad-opds-books</id>\n"
                   "    <updated>2025-07-12T12:00:00Z</updated>\n"
                   "    <link rel=\"http://opds-spec.org/catalog\" "
                   "type=\"application/atom+xml;profile=opds-catalog;kind=acquisition\" "
                   "href=\"" + absURL("/opds/books.xml") + "\"/>\n"
                   "  </entry>\n");

    opdsWrite(res, "</feed>");
    request->send(res);
}

void handleOPDSBooks(AsyncWebServerRequest *request) {
    Serial.println("[OPDS] === handleOPDSBooks() called ===");
    // full recursive walk of /Books, so wait for the card like every other reader
    if (sdMutex && xSemaphoreTake(sdMutex, pdMS_TO_TICKS(2000)) != pdTRUE) {
      request->send(503, "text/plain", "SD busy");
      return;
    }
    AsyncResponseStream *res =
        request->beginResponseStream(
            "application/atom+xml;profile=opds-catalog;kind=acquisition");

    opdsWrite(res,"<?xml version=\"1.0\" encoding=\"utf-8\"?>\n"
                  "<feed xmlns=\"http://www.w3.org/2005/Atom\" "
                  "xmlns:opds=\"http://opds-spec.org/2010/catalog\">\n");
    opdsWrite(res,
      "  <id>urn:uuid:nomad-opds-books</id>\n"
      "  <title>All Books</title>\n"
      "  <updated>"+rfc3339Now()+"</updated>\n"
      "  <link rel=\"self\"  href=\""+absURL("/opds/books.xml")+"\" "
      "type=\"application/atom+xml;profile=opds-catalog;kind=acquisition\"/>\n"
      "  <link rel=\"start\" href=\""+absURL("/opds/root.xml")+"\" "
      "type=\"application/atom+xml;profile=opds-catalog;kind=navigation\"/>\n");

    std::function<void(const String&)> processDir = [&](const String& dirPath) {
      File dir = SD_MMC.open(dirPath);
      if (!dir || !dir.isDirectory()) {
        if (dir) dir.close();
        return;
      }
      
      dir.rewindDirectory();
      while (true) {
        File file = dir.openNextFile();
        if (!file) break;

        // name() returns the bare entry name, so build the real path from the directory
        // being walked. using name() as a path broke recursion into subfolders
        String fileName = String(file.name());
        int lastSlash = fileName.lastIndexOf('/');
        if (lastSlash >= 0) fileName = fileName.substring(lastSlash + 1);
        String fullPath = dirPath + (dirPath.endsWith("/") ? "" : "/") + fileName;
        
        if (file.isDirectory()) {
          if (isComicFolder(fullPath)) {
            String base = fileName;
            String safeTitle = xmlEscape(base);
            String safeId = "urn:uuid:nomad-comic-" + slugify(base);
            
            String coverPath = "placeholder.jpg";
            File comicDir = SD_MMC.open(fullPath);
            if (comicDir && comicDir.isDirectory()) {
              comicDir.rewindDirectory();
              File firstImg;
              while ((firstImg = comicDir.openNextFile())) {
                if (!firstImg.isDirectory()) {
                  String imgName = String(firstImg.name());
                  imgName.toLowerCase();
                  if (imgName.endsWith(".jpg") || imgName.endsWith(".png") || imgName.endsWith(".jpeg")) {
                    coverPath = fullPath.substring(1) + "/" + String(firstImg.name()).substring(String(firstImg.name()).lastIndexOf('/') + 1);
                    firstImg.close();
                    break;
                  }
                }
                firstImg.close();
              }
              comicDir.close();
            }
            
            opdsWrite(res,"  <entry>\n"
                          "    <title>"+safeTitle+" [Comic]</title>\n"
                          "    <id>"+safeId+"</id>\n"
                          "    <updated>"+rfc3339Now()+"</updated>\n"
                          "    <link rel=\"http://opds-spec.org/image/thumbnail\" "
                          "type=\"image/jpeg\" href=\""+absURL("/"+urlencode(coverPath))+"\"/>\n"
                          "    <link rel=\"alternate\" "
                          "type=\"text/html\" "
                          "href=\"" + absURL("/comicreader.html?path=" + urlencode(fullPath)) + "\"/>\n"
                          "  </entry>\n");
          } else {
            processDir(fullPath);
          }
          file.close();
          continue;
        }
        
        String fnLower = fileName;
        fnLower.toLowerCase();
        
        if (!(fnLower.endsWith(".epub") || fnLower.endsWith(".pdf"))) {
          file.close();
          continue;
        }
        
        String base = fileName.substring(0, fileName.lastIndexOf('.'));
        String safeTitle = xmlEscape(base);
        String safeId = "urn:uuid:nomad-book-" + slugify(base);
        String mime = fnLower.endsWith(".epub") ? "application/epub+zip" : "application/pdf";
        
        String parentPath = fullPath.substring(0, fullPath.lastIndexOf('/'));
        String coverPath = parentPath + "/" + base + ".jpg";
        if (!SD_MMC.exists(coverPath)) {
          coverPath = "placeholder.jpg";
        } else {
          coverPath = coverPath.substring(1);
        }
        
        String ext = fnLower.endsWith(".pdf") ? ".pdf" : ".epub";
        String dlPath = fullPath;
        
        opdsWrite(res,"  <entry>\n"
                      "    <title>"+safeTitle+"</title>\n"
                      "    <id>"+safeId+"</id>\n"
                      "    <updated>"+rfc3339Now()+"</updated>\n"
                      "    <link rel=\"http://opds-spec.org/image/thumbnail\" "
                      "type=\"image/jpeg\" href=\""+absURL("/"+urlencode(coverPath))+"\"/>\n"
                      "    <link rel=\"http://opds-spec.org/acquisition\" "
                      "type=\""+mime+"\" "
                      "href=\"" + absURL(dlPath) + "\"/>\n"
                      "  </entry>\n");
        
        file.close();
      }
      
      dir.close();
    };
    
    processDir("/Books");

    if (sdMutex) xSemaphoreGive(sdMutex);
    opdsWrite(res,"</feed>");
    request->send(res);
}
String urlDecode(const String& str) {
    String decoded = "";
    char temp[] = "0x00";
    for (unsigned int i = 0; i < str.length(); i++) {
        if (str[i] == '%') {
            if (i + 2 < str.length()) {
                temp[2] = str[i+1];
                temp[3] = str[i+2];
                decoded += (char) strtol(temp, NULL, 16);
                i += 2;
            }
        } else if (str[i] == '+') {
            decoded += ' ';
        } else {
            decoded += str[i];
        }
    }
    return decoded;
}

#include <map>
#include <set>
#include <utility> // for std::pair

void handleRangeRequest(AsyncWebServerRequest *request) {
  if (indexingTasksActive) {
    Serial.println("[RangeHandler] Blocked: indexing in progress");
    request->send(503, "text/plain", "Indexing in progress. Please wait...");
    return;
  }

  String filePath;
  if (request->hasParam("file")) {
    filePath = request->getParam("file")->value();
  } else {
    filePath = urlDecode(request->url());
  }

  if (!filePath.startsWith("/")) filePath = "/" + filePath;
  filePath = normalizePath(filePath);

  // OPTIMIZATION: Reduce mutex timeout from 5000ms to 1000ms
  if (sdMutex) {
    if (xSemaphoreTake(sdMutex, pdMS_TO_TICKS(1000)) != pdTRUE) {
      Serial.printf("[RangeHandler] SD mutex timeout for: %s\n", filePath.c_str());
      request->send(503, "text/plain", "SD busy — retrying shortly");
      return;
    }
  }

  auto releaseSd = [&](){
    if (sdMutex) xSemaphoreGive(sdMutex);
  };

  bool fileExists = SD_MMC.exists(filePath);

  if (!fileExists) {
    Serial.printf("[RangeHandler] File not found: %s\n", filePath.c_str());
    releaseSd();
    request->send(404, "text/plain", "File not found");
    return;
  }

  // 64-bit stat: fs::File::size() truncates modulo 4 GB, which would report a
  // 5 GB file as 0.88 GB and reject every range past 4 GB.
  uint64_t fileSize = SD_MMC.fileSize64(filePath.c_str());
  releaseSd();

  if (fileSize == 0) {
    // could be a genuinely empty file, a directory, or an open failure - the
    // exists() check above already passed, so treat it as unreadable
    Serial.printf("[SD] size query failed or empty: '%s'\n", filePath.c_str());
    sdErrorFlag = true;
    sdErrorCooldownUntil = millis() + 5000;
    request->send(503, "text/plain", "SD error");
    return;
  }

  if (request->method() == HTTP_HEAD) {
    AsyncWebServerResponse *headResponse = request->beginResponse(200, "application/octet-stream", "");
    headResponse->addHeader("Accept-Ranges", "bytes");
    headResponse->addHeader("Content-Length", String(fileSize));
    headResponse->addHeader("Cache-Control", "public, max-age=3600");
    headResponse->addHeader("Pragma", "no-cache");
    // DLNA players often probe with HEAD before playing
    headResponse->addHeader("transferMode.dlna.org", "Streaming");
    headResponse->addHeader("contentFeatures.dlna.org", "DLNA.ORG_OP=01;DLNA.ORG_CI=0;DLNA.ORG_FLAGS=01700000000000000000000000000000");
    request->send(headResponse);
    return;
  }

  String rangeHeader = "";
  if (request->hasHeader("Range")) rangeHeader = request->header("Range");

  uint64_t startByte = 0;
  uint64_t endByte = fileSize - 1;
  bool openEndedRange = false;

  if (rangeHeader.length() && rangeHeader.startsWith("bytes=")) {
    int dashIndex = rangeHeader.indexOf('-');
    // "bytes=-N" asks for the last N bytes, not the first N. reading it as start 0
    // end N served the head of the file under a 206 that said otherwise
    bool suffixRange = (dashIndex == 6);
    // strtoull, not strtoul/toInt(): offsets into a >4 GB exFAT file need 64 bits
    if (dashIndex > 6) {
      startByte = (uint64_t)strtoull(rangeHeader.substring(6, dashIndex).c_str(), nullptr, 10);
    }
    if (dashIndex + 1 < rangeHeader.length()) {
      String endStr = rangeHeader.substring(dashIndex + 1);
      if (endStr.length() > 0) {
        uint64_t v = (uint64_t)strtoull(endStr.c_str(), nullptr, 10);
        if (suffixRange) {
          startByte = (v >= fileSize) ? 0 : (fileSize - v);
          endByte = fileSize - 1;
        } else {
          endByte = v;
        }
      } else {
        openEndedRange = true;
      }
    } else {
      openEndedRange = true;
    }
  }

  if (openEndedRange && (endByte - startByte) > (8ULL * 1024 * 1024)) {
    endByte = startByte + (8ULL * 1024 * 1024) - 1;
  }

  if (startByte >= fileSize) {
    // RFC 9110: a start beyond EOF must be refused, not clamped
    AsyncWebServerResponse *r416 = request->beginResponse(416, "text/plain", "Range not satisfiable");
    r416->addHeader("Content-Range", "bytes */" + String(fileSize));
    request->send(r416);
    return;
  }
  if (endByte >= fileSize) endByte = fileSize - 1;
  if (startByte > endByte) startByte = endByte;

  // A response body must fit size_t, so cap any single reply. Returning fewer bytes
  // than asked is legal as long as Content-Range says so.
  const uint64_t MAX_RESPONSE_BYTES = 256ULL * 1024 * 1024;
  if (endByte - startByte + 1 > MAX_RESPONSE_BYTES) {
    endByte = startByte + MAX_RESPONSE_BYTES - 1;
  }
  size_t contentLength = (size_t)(endByte - startByte + 1);
  // a plain GET of a file too big for one body degrades to partial content
  bool forcedPartial = (rangeHeader.length() == 0) && (endByte + 1 < fileSize);

  String mimeType = "application/octet-stream";
  String pLower = filePath;
  pLower.toLowerCase();

  bool isMediaStream = false;
  if (pLower.endsWith(".epub")) mimeType = "application/epub+zip";
  else if (pLower.endsWith(".pdf")) mimeType = "application/pdf";
  else if (pLower.endsWith(".mp3")) { mimeType = "audio/mpeg"; isMediaStream = true; }
  else if (pLower.endsWith(".flac")) { mimeType = "audio/flac"; isMediaStream = true; }
  else if (pLower.endsWith(".wav")) { mimeType = "audio/wav"; isMediaStream = true; }
  else if (pLower.endsWith(".ogg")) { mimeType = "audio/ogg"; isMediaStream = true; }
  else if (pLower.endsWith(".aac")) { mimeType = "audio/aac"; isMediaStream = true; }
  else if (pLower.endsWith(".m4a")) { mimeType = "audio/mp4"; isMediaStream = true; }
  else if (pLower.endsWith(".mp4")) { mimeType = "video/mp4"; isMediaStream = true; }
  else if (pLower.endsWith(".webm")) { mimeType = "video/webm"; isMediaStream = true; }
  else if (pLower.endsWith(".m4v")) { mimeType = "video/x-m4v"; isMediaStream = true; }
  else if (pLower.endsWith(".jpg") || pLower.endsWith(".jpeg")) mimeType = "image/jpeg";
  else if (pLower.endsWith(".png")) mimeType = "image/png";
  else if (pLower.endsWith(".webp")) mimeType = "image/webp";
  else if (pLower.endsWith(".gif")) mimeType = "image/gif";
  else if (pLower.endsWith(".bmp")) mimeType = "image/bmp";
  else if (pLower.endsWith(".avif")) mimeType = "image/avif";
  else if (pLower.endsWith(".cbz")) mimeType = "application/vnd.comicbook+zip";
  else if (pLower.endsWith(".cbr")) mimeType = "application/vnd.comicbook-rar";

  if (isMediaStream && startByte < 65536) {
    String fileName = filePath.substring(filePath.lastIndexOf('/') + 1);
    webLog("Playing: " + fileName + " (" + humanSize(fileSize) + ") [Media]", "media");
  }

  if (isMediaStream && contentLength > 10000) {
    mediaStreamingActive = true;
    lastStreamIoMs = millis();
    shutdownBackgroundTasksForStreaming();
  }

  if (pLower.indexOf("/archive/") >= 0) {
    mediaStreamingActive = true;
    lastStreamIoMs = millis();
    shutdownBackgroundTasksForStreaming();
  }

  uint32_t streamId = 0;
  if (streamingFilesMutex && xSemaphoreTake(streamingFilesMutex, pdMS_TO_TICKS(300)) == pdTRUE) {

    bool sdHeld = (!sdMutex) || (xSemaphoreTake(sdMutex, pdMS_TO_TICKS(2000)) == pdTRUE);
    if (!sdHeld) {
      xSemaphoreGive(streamingFilesMutex);
      request->send(503, "text/plain", "SD busy");
      return;
    }
    auto pidx = streamPathIndex.find(filePath);
    if (pidx != streamPathIndex.end()) {
      uint32_t existingId = pidx->second;
      auto eit = streamingFiles.find(existingId);

      // The old stack needed a "reopen instead of seek past 2 GB" guard here, because
      // fs::File sat on newlib stdio and its signed 32-bit offset corrupted the FILE
      // buffer on a reused handle. SdFat seeks 64-bit natively.
      if (eit != streamingFiles.end() && eit->second.file.isOpen()) {
        eit->second.file.seek(startByte);
        eit->second.lastActivity = millis();
        eit->second.lastEndByte = endByte;
        streamId = existingId;
        Serial.printf("[Stream] Reuse #%u seek %llu: %s (heap=%u)\n",
                      streamId, (unsigned long long)startByte, filePath.c_str(),
                      (unsigned)ESP.getFreeHeap());
        if (sdMutex) xSemaphoreGive(sdMutex);
        xSemaphoreGive(streamingFilesMutex);
        goto stream_ready;
      } else {
        streamPathIndex.erase(pidx);
        if (eit != streamingFiles.end()) streamingFiles.erase(eit);
      }
    }

    bool isArchive = (filePath.indexOf("/Archive/") >= 0) || (filePath.indexOf("/archive/") >= 0);
    if (isArchive) {
      for (auto ait = streamingFiles.begin(); ait != streamingFiles.end(); ) {
        const String &ap = ait->second.path;
        if (ap.indexOf("/Archive/") >= 0 || ap.indexOf("/archive/") >= 0) {
          Serial.printf("[Stream] Archive single-handle: closing #%u (%s)\n", ait->first, ap.c_str());
          streamPathIndex.erase(ait->second.path);
          ait->second.file.close();
          ait = streamingFiles.erase(ait);
        } else {
          ++ait;
        }
      }
    }

    if ((int)streamingFiles.size() >= MAX_CONCURRENT_STREAMS) {
      uint32_t oldestId = 0;
      unsigned long oldestTime = 0xFFFFFFFFUL;
      for (auto &kv : streamingFiles) {
        if (kv.second.lastActivity < oldestTime) {
          oldestTime = kv.second.lastActivity;
          oldestId = kv.first;
        }
      }
      if (oldestId) {
        auto it = streamingFiles.find(oldestId);
        if (it != streamingFiles.end()) {
          Serial.printf("[Stream] Evicting #%u (%s)\n", oldestId, it->second.path.c_str());
          streamPathIndex.erase(it->second.path);
          it->second.file.close();
          streamingFiles.erase(it);
        }
      }
    }

    StreamHandle sh;
    if (!sh.file.open(filePath.c_str())) {
      Serial.printf("[Stream] Failed to open: %s\n", filePath.c_str());
      if (sdMutex) xSemaphoreGive(sdMutex);
      xSemaphoreGive(streamingFilesMutex);
      request->send(503, "text/plain", "Failed to open file");
      return;
    }
    sh.file.seek(startByte);
    streamId = nextStreamId++;
    if (nextStreamId == 0) nextStreamId = 1;
    sh.path = filePath;
    sh.lastActivity = millis();
    sh.lastEndByte = endByte;
    streamingFiles[streamId] = std::move(sh);  // NomadFile64 is move-only
    streamPathIndex[filePath] = streamId;
    activeStreams = streamingFiles.size();
    Serial.printf("[Stream] New #%u at %llu: %s (active=%d heap=%u)\n",
                  streamId, (unsigned long long)startByte, filePath.c_str(), activeStreams,
                  (unsigned)ESP.getFreeHeap());
    if (sdMutex) xSemaphoreGive(sdMutex);
    xSemaphoreGive(streamingFilesMutex);
  } else {
    Serial.printf("[Stream] Mutex timeout for: %s\n", filePath.c_str());
    request->send(503, "text/plain", "Server busy");
    return;
  }

  stream_ready:

  // Read position for this response. streamPathIndex hands the same handle to every
  // request for a path, so two clients playing one file used to read through one
  // shared position. Each response seeks to its own offset first.
  auto streamPos = std::make_shared<uint64_t>(startByte);

  AsyncWebServerResponse *response = request->beginResponse(
    mimeType,
    contentLength,
    [streamId, streamPos, filePath, startByte](uint8_t *buffer, size_t maxLen, size_t index) -> size_t {
      // busy mutex isnt end-of-data: returning 0 truncates the response, TRY_AGAIN retries later
      if (streamingFilesMutex && xSemaphoreTake(streamingFilesMutex, pdMS_TO_TICKS(150)) != pdTRUE) {
        return RESPONSE_TRY_AGAIN;
      }

      auto it = streamingFiles.find(streamId);
      if (it == streamingFiles.end()) {
        // evicted mid-send. returning 0 would look like end-of-body and truncate
        // the response (browser sees NS_ERROR_NET_RESET), so reopen and resume.
        bool sdHeld = (!sdMutex) || (xSemaphoreTake(sdMutex, pdMS_TO_TICKS(1000)) == pdTRUE);
        if (!sdHeld) {
          xSemaphoreGive(streamingFilesMutex);
          return RESPONSE_TRY_AGAIN;
        }
        // ported to NomadSD: open() takes a path and answers bool, and the handle is a
        // NomadFile64, not an fs::File - main's version was written against SD_MMC.
        // built in place because a StreamHandle owns its file and cannot be copied.
        StreamHandle &sh = streamingFiles[streamId];
        if (!sh.file.open(filePath.c_str())) {
          streamingFiles.erase(streamId);
          if (sdMutex) xSemaphoreGive(sdMutex);
          xSemaphoreGive(streamingFilesMutex);
          Serial.printf("[Stream] Reopen failed for #%u (%s) - truncating\n",
                        streamId, filePath.c_str());
          return 0;  // genuinely unrecoverable
        }
        sh.file.seek(startByte + index);
        sh.path = filePath;
        sh.lastActivity = millis();
        sh.lastEndByte = startByte + index;
        streamPathIndex[filePath] = streamId;
        if (sdMutex) xSemaphoreGive(sdMutex);
        Serial.printf("[Stream] Reopened #%u at %lu (evicted mid-send): %s\n",
                      streamId, (unsigned long)(startByte + index), filePath.c_str());
        it = streamingFiles.find(streamId);
      }

      NomadFile64 &file = it->second.file;
      it->second.lastActivity = millis();
      lastStreamIoMs = it->second.lastActivity;

      size_t toRead = maxLen;
      if (toRead > 16384) toRead = 16384;

      size_t bytesRead = 0;
      bool sdBusy = false;
      if (!sdMutex) {
        bytesRead = file.readAt(*streamPos, buffer, toRead);
        *streamPos += bytesRead;
      } else if (xSemaphoreTake(sdMutex, pdMS_TO_TICKS(1500)) == pdTRUE) {
        // readAt keeps the seek and the read in one lock acquisition, so another
        // reader of the same file cannot move the handle in between
        bytesRead = file.readAt(*streamPos, buffer, toRead);
        *streamPos += bytesRead;
        xSemaphoreGive(sdMutex);
      } else {
        sdBusy = true;  // transient: retry this fill later, don't truncate
      }
      xSemaphoreGive(streamingFilesMutex);

      return sdBusy ? RESPONSE_TRY_AGAIN : bytesRead;
    }
  );

  // beginResponse answers NULL on low heap, and dereferencing it panics async_tcp and
  // takes the server down with it. closeStreamById gives back the handle this response
  // would have owned, so a refused stream doesn't sit there until the LRU reaps it.
  if (!response) {
    Serial.printf("[Stream] beginResponse OOM for %s (heap=%u)\n",
                  filePath.c_str(), (unsigned)ESP.getFreeHeap());
    closeStreamById(streamId);
    request->send(503, "text/plain", "Server low on memory - retry");
    return;
  }

  if (rangeHeader.length() > 0 || forcedPartial) {
    // forcedPartial: no Range was sent but the file is too big for one body, so
    // answer 206 with an honest Content-Range instead of a truncated 200
    response->setCode(206);
    response->addHeader("Content-Range", "bytes " + String(startByte) + "-" + String(endByte) + "/" + String(fileSize));
  } else {
    response->setCode(200);
  }

  response->addHeader("Access-Control-Allow-Origin", "*");
  response->addHeader("Access-Control-Allow-Methods", "GET, HEAD, OPTIONS");
  response->addHeader("Access-Control-Allow-Headers", "Range, Content-Type, Accept");
  response->addHeader("Accept-Ranges", "bytes");
  response->addHeader("Content-Length", String(contentLength));
  response->addHeader("Cache-Control", "public, max-age=3600");
  response->addHeader("Connection", "close");
  if (isMediaStream) {
    // DLNA players need these on the stream itself. Samsung refuses to play without
    // transferMode + contentFeatures, LG will not seek without realTimeInfo.
    response->addHeader("transferMode.dlna.org", "Streaming");
    response->addHeader("contentFeatures.dlna.org", "DLNA.ORG_OP=01;DLNA.ORG_CI=0;DLNA.ORG_FLAGS=01700000000000000000000000000000");
    response->addHeader("realTimeInfo.dlna.org", "DLNA.ORG_TLAG=*");
  }
  request->send(response);
}
void handleListFiles(AsyncWebServerRequest *request) {
    if (!request->hasParam("dir")) {
        request->send(400, "application/json", "{\"error\":\"Missing 'dir' parameter\"}");
        return;
    }
    String dir = request->getParam("dir")->value();

    // chat and the live whiteboard poll this every couple of seconds, so it has
    // to fail fast rather than wait on the SdFat lock with no timeout
    if (sdMutex && xSemaphoreTake(sdMutex, pdMS_TO_TICKS(1000)) != pdTRUE) {
        request->send(503, "application/json", "{\"error\":\"SD busy\"}");
        return;
    }
    auto listDone = [&]() { if (sdMutex) xSemaphoreGive(sdMutex); };

    if (!SD_MMC.exists(dir)) {
        listDone();
        request->send(404, "application/json", "{\"error\":\"Directory not found\"}");
        return;
    }

    File directory = SD_MMC.open(dir);
    if (!directory || !directory.isDirectory()) {
        if (directory) directory.close();
        listDone();
        request->send(404, "application/json", "{\"error\":\"Not a directory\"}");
        return;
    }

    // ArduinoJson 7 grows a document from the heap on demand: the number handed to
    // DynamicJsonDocument is remembered and reported by capacity(), but it does not
    // bound anything, and overflowed() only goes true on a real allocation failure.
    // So the ceiling here is the ESP32's heap, and the whole response also has to fit
    // in one String below. Bound it ourselves, generously, and say when we did.
    static const size_t LIST_MAX_BYTES = 49152;   // ~800 entries, far past any real folder
    DynamicJsonDocument doc(LIST_MAX_BYTES);
    JsonArray arr = doc.to<JsonArray>();
    bool truncated = false;
    size_t approxBytes = 2;                       // the enclosing []

    File file = directory.openNextFile();
    while (file) {
        JsonObject f = arr.createNestedObject();

        String filename = String(file.name());
        // Strip dir prefix
        if (filename.startsWith(dir)) {
            filename = filename.substring(dir.length());
            if (filename.startsWith("/")) filename = filename.substring(1);
        }

        if (file.isDirectory()) {
            // Append slash to indicate directory
            f["name"] = filename + "/";
            f["size"] = 0;
            f["isDir"] = true;
        } else {
            f["name"] = filename;
            uint64_t fsz = (uint64_t)file.size();
            if (fsz == (uint64_t)SIZE_MAX) fsz = SD_MMC.fileSize64(file.path());
            f["size"] = fsz;
            f["isDir"] = false;
        }
        // {"name":"...","size":N,"isDir":false} plus the separator, near enough
        approxBytes += filename.length() + 48;

        file = directory.openNextFile();
        if (approxBytes > LIST_MAX_BYTES) { truncated = true; break; }
        if (doc.overflowed()) { truncated = true; break; }   // heap actually ran out
        yield();
    }
    if (file) file.close();   // breaking out of the loop leaves the handle open

    // A marker entry rather than a header, because the response is a bare array.
    // Callers that ignore it see the same list they always did; callers that read
    // it know to go to the (uncapped) NDJSON index for the full listing.
    if (truncated) {
        JsonObject t = arr.createNestedObject();
        t["name"] = "";
        t["truncated"] = true;
        Serial.printf("[ListFiles] '%s' truncated at %u entries\n", dir.c_str(), (unsigned)(arr.size() - 1));
    }

    // Serialize and send
    String response;
    serializeJson(arr, response);
    directory.close();
    listDone();
    request->send(200, "application/json", response);
}

// ------------------------- ARCHIVE MANIFEST -------------------------
String escapeJsonString(const String &in) {
  String out;
  out.reserve(in.length());
  for (size_t i = 0; i < in.length(); ++i) {
    char c = in.charAt(i);
    if (c == '\\' || c == '\"') {
      out += '\\';
      out += c;
    } else if (c == '\b') out += "\\b";
    else if (c == '\f') out += "\\f";
    else if (c == '\n') out += "\\n";
    else if (c == '\r') out += "\\r";
    else if (c == '\t') out += "\\t";
    else out += c;
  }
  return out;
}

static String archiveTypeForExt(const String &lowerName) {
  if (lowerName.endsWith(".zim")) return "zim";
  // .zimaa .. .zimzz split parts
  int len = lowerName.length();
  if (len > 6 && lowerName.lastIndexOf(".zim") == len - 6) {
    char a = lowerName.charAt(len - 2), b = lowerName.charAt(len - 1);
    if (a >= 'a' && a <= 'z' && b >= 'a' && b <= 'z') return "zim";
  }
  if (lowerName.endsWith(".mbtiles")) return "maps";     // future: map tiles
  if (lowerName.endsWith(".nes") || lowerName.endsWith(".sfc") || lowerName.endsWith(".smc") ||
      lowerName.endsWith(".gb")  || lowerName.endsWith(".gbc") || lowerName.endsWith(".gba") ||
      lowerName.endsWith(".md")  || lowerName.endsWith(".z64")) return "rom"; // future: EmulatorJS
  return "file";
}

void handleArchiveList(AsyncWebServerRequest *request) {
  struct ArchivePart { String path; uint64_t size; };
  struct ArchiveGroup { String id; String type; bool split; std::vector<ArchivePart> parts; };
  std::vector<ArchiveGroup> groups;

  bool sdLocked = false;
  if (sdMutex) {
    if (xSemaphoreTake(sdMutex, pdMS_TO_TICKS(1000)) != pdTRUE) {
      request->send(503, "application/json", "{\"error\":\"SD busy\"}");
      return;
    }
    sdLocked = true;
  }

  File root = SD_MMC.open("/Archive");
  if (!root || !root.isDirectory()) {
    if (root) root.close();
    if (sdLocked) xSemaphoreGive(sdMutex);
    // No /Archive folder is a normal setup, not an error: empty manifest.
    AsyncWebServerResponse *r = request->beginResponse(200, "application/json", "{\"archives\":[]}");
    r->addHeader("Access-Control-Allow-Origin", "*");
    request->send(r);
    return;
  }

  int fileCount = 0;
  File file = root.openNextFile();
  while (file && fileCount < 128) {
    if (!file.isDirectory()) {
      fileCount++;
      String name = String(file.name());
      int slash = name.lastIndexOf('/');
      if (slash >= 0) name = name.substring(slash + 1);
      if (!name.startsWith(".")) {
        String lower = name;
        lower.toLowerCase();
        String type = archiveTypeForExt(lower);

        // id = filename minus extension; split parts (.zimaa) drop the suffix too so they share one id
        String id = name;
        bool isSplitPart = false;
        int len = lower.length();
        if (type == "zim" && len > 6 && lower.lastIndexOf(".zim") == len - 6 && !lower.endsWith(".zim")) {
          isSplitPart = true;
          id = name.substring(0, len - 6);
        } else {
          int dot = id.lastIndexOf('.');
          if (dot > 0) id = id.substring(0, dot);
        }

        ArchiveGroup *g = nullptr;
        for (auto &existing : groups) {
          if (existing.id == id && existing.type == type) { g = &existing; break; }
        }
        if (!g) {
          groups.push_back(ArchiveGroup{ id, type, false, {} });
          g = &groups.back();
        }
        if (isSplitPart) g->split = true;
        // size() saturates at SIZE_MAX past 4 GB and means "ask fileSize64". a single ZIM
        // over 4 GB is the reason the exFAT build exists
        uint64_t psz = (uint64_t)file.size();
        if (psz == (uint64_t)SIZE_MAX) psz = SD_MMC.fileSize64(file.path());
        g->parts.push_back(ArchivePart{ String("/Archive/") + name, psz });
      }
    }
    file.close();
    file = root.openNextFile();
    yield();
  }
  root.close();
  if (sdLocked) xSemaphoreGive(sdMutex);

  String resp; resp.reserve(12 * 1024);   // ~128 parts at ~90B each, no realloc churn
  resp = "{\"archives\":[";
  bool firstGroup = true;
  for (auto &g : groups) {
    // Alphabetical part order == byte order for zimsplit suffixes.
    std::sort(g.parts.begin(), g.parts.end(),
              [](const ArchivePart &a, const ArchivePart &b) { return a.path < b.path; });
    uint64_t total = 0;
    for (auto &p : g.parts) total += p.size;

    if (!firstGroup) resp += ",";
    firstGroup = false;
    resp += "{\"id\":\"" + escapeJsonString(g.id) + "\",\"name\":\"" + escapeJsonString(g.id) + "\"";
    resp += ",\"type\":\"" + g.type + "\",\"split\":" + (g.split ? "true" : "false");
    resp += ",\"totalSize\":" + String((unsigned long long)total) + ",\"parts\":[";
    bool firstPart = true;
    for (auto &p : g.parts) {
      if (!firstPart) resp += ",";
      firstPart = false;
      resp += "{\"path\":\"" + escapeJsonString(p.path) + "\",\"size\":" + String((unsigned long long)p.size) + "}";
    }
    resp += "]}";
  }
  resp += "]}";

  AsyncWebServerResponse *r = request->beginResponse(200, "application/json", resp);
  r->addHeader("Access-Control-Allow-Origin", "*");
  request->send(r);
  Serial.printf("[ARCHIVE] /api/archive-list: %d group(s), %u bytes\n", (int)groups.size(), (unsigned)resp.length());
}

// Cheap directory scan so menu.html can reveal the Games tile only when /Games has
// content. same pattern as handleArchiveList, reads no file content.
void handleGamesList(AsyncWebServerRequest *request) {
  bool sdLocked = false;
  if (sdMutex) {
    if (xSemaphoreTake(sdMutex, pdMS_TO_TICKS(1000)) != pdTRUE) {
      request->send(503, "application/json", "{\"error\":\"SD busy\"}");
      return;
    }
    sdLocked = true;
  }

  File root = SD_MMC.open("/Games");
  if (!root || !root.isDirectory()) {
    if (root) root.close();
    if (sdLocked) xSemaphoreGive(sdMutex);
    AsyncWebServerResponse *r = request->beginResponse(200, "application/json", "{\"games\":[]}");
    r->addHeader("Access-Control-Allow-Origin", "*");
    request->send(r);
    return;
  }

  String resp; resp.reserve(24 * 1024);   // ~256 entries at ~90B each, no realloc churn
  resp = "{\"games\":[";
  bool first = true;
  int fileCount = 0;
  File file = root.openNextFile();
  while (file && fileCount < 256) {
    if (!file.isDirectory()) {
      String name = String(file.name());
      int slash = name.lastIndexOf('/');
      if (slash >= 0) name = name.substring(slash + 1);
      // Skip dotfiles and sibling cover art -- only ROM files count toward "has content".
      String lower = name;
      lower.toLowerCase();
      if (!name.startsWith(".") && !lower.endsWith(".png") && !lower.endsWith(".jpg") && !lower.endsWith(".jpeg")) {
        fileCount++;
        if (!first) resp += ",";
        first = false;
        resp += "{\"name\":\"" + escapeJsonString(name) + "\",\"path\":\"/Games/" + escapeJsonString(name) + "\"";
        resp += ",\"size\":" + String((unsigned long long)file.size()) + "}";
      }
    }
    file.close();
    file = root.openNextFile();
    yield();
  }
  root.close();
  if (sdLocked) xSemaphoreGive(sdMutex);

  resp += "]}";
  AsyncWebServerResponse *r = request->beginResponse(200, "application/json", resp);
  r->addHeader("Access-Control-Allow-Origin", "*");
  request->send(r);
  Serial.printf("[GAMES] /api/games-list: %d file(s), %u bytes\n", fileCount, (unsigned)resp.length());
}

// Cheap directory scan for menu.html's Maps tile: region subfolders under /Maps that
// have a manifest.json. per-region detail is fetched by the client, not parsed here.
void handleMapsList(AsyncWebServerRequest *request) {
  bool sdLocked = false;
  if (sdMutex) {
    if (xSemaphoreTake(sdMutex, pdMS_TO_TICKS(1000)) != pdTRUE) {
      request->send(503, "application/json", "{\"error\":\"SD busy\"}");
      return;
    }
    sdLocked = true;
  }

  File root = SD_MMC.open("/Maps");
  if (!root || !root.isDirectory()) {
    if (root) root.close();
    if (sdLocked) xSemaphoreGive(sdMutex);
    AsyncWebServerResponse *r = request->beginResponse(200, "application/json", "{\"regions\":[]}");
    r->addHeader("Access-Control-Allow-Origin", "*");
    request->send(r);
    return;
  }

  String resp; resp.reserve(6 * 1024);    // ~64 regions, no realloc churn
  resp = "{\"regions\":[";
  bool first = true;
  int regionCount = 0;
  File entry = root.openNextFile();
  while (entry && regionCount < 64) {
    if (entry.isDirectory()) {
      String name = String(entry.name());
      int slash = name.lastIndexOf('/');
      if (slash >= 0) name = name.substring(slash + 1);
      if (!name.startsWith(".")) {
        String manifestPath = "/Maps/" + name + "/manifest.json";
        if (SD_MMC.exists(manifestPath)) {
          regionCount++;
          if (!first) resp += ",";
          first = false;
          resp += "{\"id\":\"" + escapeJsonString(name) + "\",\"manifest\":\"" + escapeJsonString(manifestPath) + "\"}";
        }
      }
    }
    entry.close();
    entry = root.openNextFile();
    yield();
  }
  root.close();
  if (sdLocked) xSemaphoreGive(sdMutex);

  resp += "]}";
  AsyncWebServerResponse *r = request->beginResponse(200, "application/json", resp);
  r->addHeader("Access-Control-Allow-Origin", "*");
  request->send(r);
  Serial.printf("[MAPS] /api/maps-list: %d region(s), %u bytes\n", regionCount, (unsigned)resp.length());
}

// ---- Multiplayer (HTTP polling) helpers -- all assume gameMutex is already held ----

static void mpGenerateCode(char *out) {  // out must be MP_CODE_LEN bytes
  static const char kAlphabet[] = "23456789ABCDEFGHJKLMNPQRSTUVWXYZ";  // no 0/O/1/I
  for (int i = 0; i < MP_CODE_LEN - 1; i++) out[i] = kAlphabet[esp_random() % (sizeof(kAlphabet) - 1)];
  out[MP_CODE_LEN - 1] = '\0';
}

static void mpGenerateToken(char *out) {  // out must be MP_TOKEN_LEN bytes
  static const char kHex[] = "0123456789abcdef";
  for (int i = 0; i < MP_TOKEN_LEN - 1; i++) out[i] = kHex[esp_random() % 16];
  out[MP_TOKEN_LEN - 1] = '\0';
}

// Reclaims any room idle past MP_ROOM_IDLE_MS. Call before allocating/looking up a room.
static void mpReapIdleRooms() {
  unsigned long now = millis();
  for (int i = 0; i < MP_MAX_ROOMS; i++) {
    if (mpRooms[i].active && (now - mpRooms[i].lastMs) > MP_ROOM_IDLE_MS) {
      Serial.printf("[MP] Reclaiming idle room '%s'\n", mpRooms[i].code);
      mpRooms[i].active = false;
    }
  }
}

static int mpFindRoomByCode(const char *code) {
  for (int i = 0; i < MP_MAX_ROOMS; i++) {
    if (mpRooms[i].active && strncmp(mpRooms[i].code, code, MP_CODE_LEN) == 0) return i;
  }
  return -1;
}

// Takes a slot index rather than a MpRoom&. Arduino's auto-generated prototypes go
// at the top of the translation unit, before the MpRoom struct, so a custom-type
// parameter here would fail to compile.
static int mpFindSeatByToken(int slot, const char *token) {
  MpRoom &room = mpRooms[slot];
  for (int seat = 0; seat < 2; seat++) {
    if (room.token[seat][0] != '\0' && strncmp(room.token[seat], token, MP_TOKEN_LEN) == 0) return seat;
  }
  return -1;
}

// POST /api/mp/create {game} -> {code, token, seat, seq}. Creator always takes seat 0.
void handleMpCreate(AsyncWebServerRequest *request, uint8_t *data, size_t len, size_t index, size_t total) {
  StaticJsonDocument<128> doc;
  if (deserializeJson(doc, data, len)) { request->send(400, "application/json", "{\"error\":\"Invalid JSON\"}"); return; }
  const char *game = doc["game"] | "";
  if (!game[0] || strlen(game) >= MP_GAME_LEN) {
    request->send(400, "application/json", "{\"error\":\"Invalid game\"}");
    return;
  }

  if (!gameMutex || xSemaphoreTake(gameMutex, pdMS_TO_TICKS(200)) != pdTRUE) {
    request->send(503, "application/json", "{\"error\":\"busy\"}");
    return;
  }

  mpReapIdleRooms();
  int slot = -1;
  for (int i = 0; i < MP_MAX_ROOMS; i++) { if (!mpRooms[i].active) { slot = i; break; } }
  if (slot < 0) {
    xSemaphoreGive(gameMutex);
    request->send(503, "application/json", "{\"error\":\"No rooms available\"}");
    return;
  }

  MpRoom &room = mpRooms[slot];
  memset(&room, 0, sizeof(room));
  char code[MP_CODE_LEN];
  int guard = 0;
  do { mpGenerateCode(code); } while (mpFindRoomByCode(code) >= 0 && ++guard < 20);
  memcpy(room.code, code, MP_CODE_LEN);
  strncpy(room.game, game, MP_GAME_LEN - 1);
  mpGenerateToken(room.token[0]);
  room.seq = 0;  // 0 = empty/waiting state; turn = seq % 2, so seat 0 moves first
  room.lastMs = millis();
  room.active = true;

  char codeOut[MP_CODE_LEN], tokenOut[MP_TOKEN_LEN];
  memcpy(codeOut, room.code, MP_CODE_LEN);
  memcpy(tokenOut, room.token[0], MP_TOKEN_LEN);
  xSemaphoreGive(gameMutex);

  String resp = String("{\"code\":\"") + codeOut + "\",\"token\":\"" + tokenOut + "\",\"seat\":0,\"seq\":0}";
  AsyncWebServerResponse *r = request->beginResponse(200, "application/json", resp);
  r->addHeader("Access-Control-Allow-Origin", "*");
  request->send(r);
  Serial.printf("[MP] Created room '%s' game=%s\n", codeOut, game);
}

// POST /api/mp/join {code} -> {token, seat}. Only seat 1 can be joined (seat 0 = creator).
void handleMpJoin(AsyncWebServerRequest *request, uint8_t *data, size_t len, size_t index, size_t total) {
  StaticJsonDocument<128> doc;
  if (deserializeJson(doc, data, len)) { request->send(400, "application/json", "{\"error\":\"Invalid JSON\"}"); return; }
  const char *code = doc["code"] | "";
  if (!code[0]) { request->send(400, "application/json", "{\"error\":\"Missing code\"}"); return; }

  if (!gameMutex || xSemaphoreTake(gameMutex, pdMS_TO_TICKS(200)) != pdTRUE) {
    request->send(503, "application/json", "{\"error\":\"busy\"}");
    return;
  }

  mpReapIdleRooms();
  int slot = mpFindRoomByCode(code);
  if (slot < 0) {
    xSemaphoreGive(gameMutex);
    request->send(404, "application/json", "{\"error\":\"Room not found\"}");
    return;
  }
  MpRoom &room = mpRooms[slot];
  if (room.token[1][0] != '\0') {
    xSemaphoreGive(gameMutex);
    request->send(409, "application/json", "{\"error\":\"Room full\"}");
    return;
  }
  mpGenerateToken(room.token[1]);
  room.lastMs = millis();
  char tokenOut[MP_TOKEN_LEN];
  memcpy(tokenOut, room.token[1], MP_TOKEN_LEN);
  xSemaphoreGive(gameMutex);

  String resp = String("{\"token\":\"") + tokenOut + "\",\"seat\":1}";
  AsyncWebServerResponse *r = request->beginResponse(200, "application/json", resp);
  r->addHeader("Access-Control-Allow-Origin", "*");
  request->send(r);
  Serial.printf("[MP] Seat 1 joined room '%s'\n", code);
}

// POST /api/mp/move {code, token, move, seq} -> {seq}. `move` is an opaque blob the
// client computed, legality is validated client side (chess.js). the server only
// enforces turn ownership (seat == seq%2) and that `seq` matches the room's current
// seq, then relays and bumps seq.
void handleMpMove(AsyncWebServerRequest *request, uint8_t *data, size_t len, size_t index, size_t total) {
  StaticJsonDocument<896> doc;  // MP_STATE_LEN (512) + code/token/seq overhead
  if (deserializeJson(doc, data, len)) { request->send(400, "application/json", "{\"error\":\"Invalid JSON\"}"); return; }
  const char *code = doc["code"] | "";
  const char *token = doc["token"] | "";
  const char *move = doc["move"] | "";
  uint32_t clientSeq = doc["seq"] | 0xFFFFFFFFu;
  if (!code[0] || !token[0]) { request->send(400, "application/json", "{\"error\":\"Missing code/token\"}"); return; }
  if (strlen(move) >= MP_STATE_LEN) { request->send(400, "application/json", "{\"error\":\"State too large\"}"); return; }

  if (!gameMutex || xSemaphoreTake(gameMutex, pdMS_TO_TICKS(200)) != pdTRUE) {
    request->send(503, "application/json", "{\"error\":\"busy\"}");
    return;
  }

  mpReapIdleRooms();
  int slot = mpFindRoomByCode(code);
  if (slot < 0) {
    xSemaphoreGive(gameMutex);
    request->send(404, "application/json", "{\"error\":\"Room not found\"}");
    return;
  }
  MpRoom &room = mpRooms[slot];
  int seat = mpFindSeatByToken(slot, token);
  if (seat < 0) {
    xSemaphoreGive(gameMutex);
    request->send(403, "application/json", "{\"error\":\"Invalid token\"}");
    return;
  }
  bool reset = doc["reset"] | false;
  if (reset) {
    // Play again: either seated player may restart with a fresh state. the turn and
    // stale-seq checks dont apply since a finished game's parity is arbitrary. rematches
    // alternate who moves first, games where rules fix it (chess) pass "first" to pin it.
    room.games++;
    int firstSeat = doc["first"] | -1;
    uint32_t wantParity = (firstSeat == 0 || firstSeat == 1) ? (uint32_t)firstSeat : (room.games % 2);
    uint32_t next = room.seq + 1;
    if (next % 2 != wantParity) next++;
    room.seq = next;
    strncpy(room.state, move, MP_STATE_LEN - 1);
    room.state[MP_STATE_LEN - 1] = '\0';
    room.lastMs = millis();
    uint32_t seqOut = room.seq;
    xSemaphoreGive(gameMutex);
    String resp = String("{\"seq\":") + seqOut + "}";
    AsyncWebServerResponse *r = request->beginResponse(200, "application/json", resp);
    r->addHeader("Access-Control-Allow-Origin", "*");
    request->send(r);
    return;
  }

  uint32_t turnSeat = room.seq % 2;
  if ((uint32_t)seat != turnSeat) {
    xSemaphoreGive(gameMutex);
    request->send(409, "application/json", "{\"error\":\"Not your turn\"}");
    return;
  }
  if (clientSeq != room.seq) {
    xSemaphoreGive(gameMutex);
    request->send(409, "application/json", "{\"error\":\"Stale seq\"}");
    return;
  }

  strncpy(room.state, move, MP_STATE_LEN - 1);
  room.state[MP_STATE_LEN - 1] = '\0';
  room.seq++;
  room.lastMs = millis();
  uint32_t seqOut = room.seq;
  xSemaphoreGive(gameMutex);

  String resp = String("{\"seq\":") + seqOut + "}";
  AsyncWebServerResponse *r = request->beginResponse(200, "application/json", resp);
  r->addHeader("Access-Control-Allow-Origin", "*");
  request->send(r);
}

// GET /api/mp/state?code=&since= -> {seq, changed, joined, state}. Short-poll target (~1s).
void handleMpState(AsyncWebServerRequest *request) {
  if (!request->hasParam("code")) { request->send(400, "application/json", "{\"error\":\"Missing code\"}"); return; }
  String codeStr = request->getParam("code")->value();
  uint32_t since = 0;
  if (request->hasParam("since")) since = (uint32_t) request->getParam("since")->value().toInt();

  if (!gameMutex || xSemaphoreTake(gameMutex, pdMS_TO_TICKS(200)) != pdTRUE) {
    request->send(503, "application/json", "{\"error\":\"busy\"}");
    return;
  }

  int slot = mpFindRoomByCode(codeStr.c_str());
  if (slot < 0) {
    xSemaphoreGive(gameMutex);
    request->send(404, "application/json", "{\"error\":\"Room not found\"}");
    return;
  }
  MpRoom &room = mpRooms[slot];
  bool changed = room.seq > since;
  bool joined = room.token[1][0] != '\0';
  uint32_t seqOut = room.seq;
  char stateOut[MP_STATE_LEN];
  memcpy(stateOut, room.state, MP_STATE_LEN);
  xSemaphoreGive(gameMutex);

  String resp = String("{\"seq\":") + seqOut + ",\"changed\":" + (changed ? "true" : "false") +
                ",\"joined\":" + (joined ? "true" : "false") +
                ",\"state\":\"" + escapeJsonString(String(stateOut)) + "\"}";
  AsyncWebServerResponse *r = request->beginResponse(200, "application/json", resp);
  r->addHeader("Access-Control-Allow-Origin", "*");
  request->send(r);
}
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
void loop() {
    if (g_enterFlashMode) {
      g_enterFlashMode = false;
      // show the message from the task that owns LVGL, on the screen already up, no
      // re-init. the ST7789 keeps its framebuffer through the reset
      lv_obj_clear_flag(ui_MediaGen, LV_OBJ_FLAG_HIDDEN);
      lv_textarea_set_text(ui_MediaGen, "Flashing Mode, Ready for Update");
      for (int i = 0; i < 6; ++i) { lv_timer_handler(); delay(30); }
      delay(150);   // let the HTTP response finish leaving the radio
      // The core's own download-mode path (same one the 1200-baud touch uses): registers a
      // shutdown handler so RTC_CNTL_FORCE_DOWNLOAD_BOOT is written last, and switches the
      // USB PHY back to the hardware JTAG/serial unit so the ROM enumerates for esptool.
      usb_persist_restart(RESTART_BOOTLOADER);
      // only reached if the shutdown-handler slot was full: set the flag by
      // hand and take a CPU-only reset, which cannot clear it on the way down
      REG_WRITE(RTC_CNTL_OPTION1_REG, RTC_CNTL_FORCE_DOWNLOAD_BOOT);
      SET_PERI_REG_MASK(RTC_CNTL_OPTIONS0_REG, RTC_CNTL_SW_PROCPU_RST);
    }
    if (bootButtonPressed) {
      bootButtonPressed = false;
      set_boot_mode(USB_MODE);
      ESP.restart();
    }
    // deferred restart after a WiFi Mode change: gives the config writer time to
    // flush settings.json and the HTTP response time to leave before rebooting
    if (g_wifiModeRestartAt && (int32_t)(millis() - g_wifiModeRestartAt) > 0) {
      g_wifiModeRestartAt = 0;
      Serial.println("[WiFiMode] Applying WiFi mode change -> restart");
      ESP.restart();
    }
    Timer_Loop();

    if (currentLEDMode == 1) {
        RGB_Lamp_Loop(2);
    }
    if (sdErrorFlag) {
        if (millis() > sdErrorCooldownUntil && tryRecoverSDCard()) {
            sdErrorFlag = false;  // we’re back in business
        } else {
            delay(5);  // keep feeding WDT while waiting
            return;    // skip rest of loop until recovery works
        }
    }
    // Check for streaming timeout to restart background tasks
    if (millis() - lastUpdateTime > 2000) {
        lastUpdateTime = millis();
        checkStreamingTimeout();
    }

    dlnaTick();  // periodic SSDP alive announcements, cheap no-op when off

    delay(10);
}


void RGB_SetMode(uint8_t mode) {
    currentLEDMode = mode;

    if (mode == 0) {
        // Turn off LED immediately
        Set_Color(0, 0, 0);
    } else if (mode == 2) {
        Set_Color(solidG, solidR, solidB);
    }
}
static unsigned long lastSweepMs = 0;
void memorySweepIfNeeded() {
  unsigned long now = millis();
  if (now - lastSweepMs < 5000) return; // run every 5s
  lastSweepMs = now;

  size_t freeHeap = ESP.getFreeHeap();
  if (freeHeap < 70000) {  //might tune this a bit 
    Serial.printf("[MEMSWEEP] low freeHeap=%u; doing sweep\n", (unsigned)freeHeap);
    yield();
  }
} 
